sayhiben/little-on-air/release/little-on-air-enclosure-v2.16/reference/README.md

# Drawing and coordinate scope

Use [front-wiring.svg](front-wiring.svg) and [routing-coordinates.json](routing-coordinates.json) for current v2.16 LED routes H1–H4. The nominal lengths are fitting references, not cut lengths. Lane numbers are not electrical pin numbers.

The historical rear coordinates are labeled separately inside the JSON; old H1–H4 coordinates are removed. Existing compact rear leads and junctions must be dressed around the current routes. Older assembly views show interfaces unchanged by v2.16; the `v216-` views show the revised parts.
