sayhiben/little-on-air/hardware/archive/enclosure/v216/README.md

# Archived enclosure v2.16

This rearward-wiring revision changes housing 05 and yoke 06, retaining the
v2.15 frame. The user kept the complete v2.15 case with open-backed frame channels
and restored it as current on September 26, 2026.

- [Current v2.15 case](../../../enclosure/README.md)
- [Preserved v2.16 release](../../../../release/little-on-air-enclosure-v2.16/README.md)
- [Preserved development outputs](../output/v216/)

The archived CAD, print files, reports and scripts retain their bytes. Some
scripts assume their former `hardware/enclosure/v216/` location. Use a separate
checkout of `de26e571f803cca94601db4a099f2a24f3e53c03` for that tooling layout.
The original one-time patch/probe scripts are preserved alongside the final
builder. Published releases and their checksum files retain their existing paths.
