sayhiben/little-on-air/hardware/archive/enclosure/archive/README.md

# Archived loose outputs

Loose generated reports moved out of the repository root during release cleanup are retained here. Historical CAD and fabrication directories keep their original paths under `../output/` because the generation scripts use some of them as inputs.

Use the [current release](../../../release/little-on-air-enclosure-v2.13/README.md) for printing, laser work and assembly.

`2026-09-14-user-layout-before-release.3mf` preserves the original edited three-plate project. It still contains the extra keeper and PETG assignment for the insert; it is historical, not the corrected release print file.
