sayhiben/little-on-air/hardware/controller/igor-desk-v1/output/views/rear.png

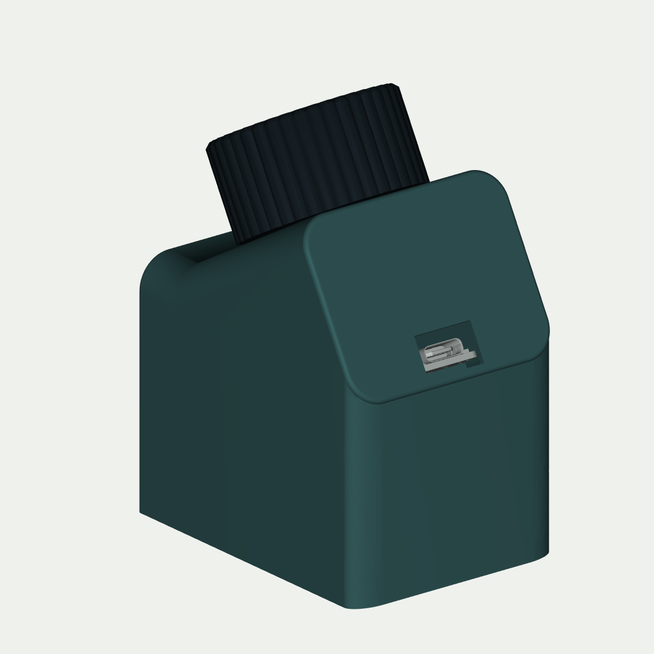
hardware/controller/igor-desk-v1/output/views/rear.png
