sayhiben/little-on-air/hardware/controller/igor-desk-v1/output/views/screen-concept.png

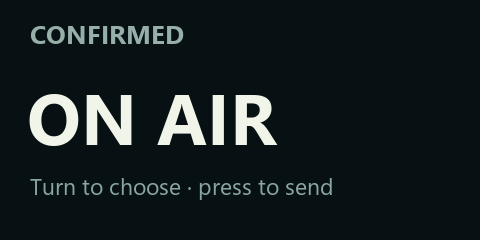
hardware/controller/igor-desk-v1/output/views/screen-concept.png
