sayhiben/little-on-air/hardware/controller/igor-desk-v1/output/views/section.png

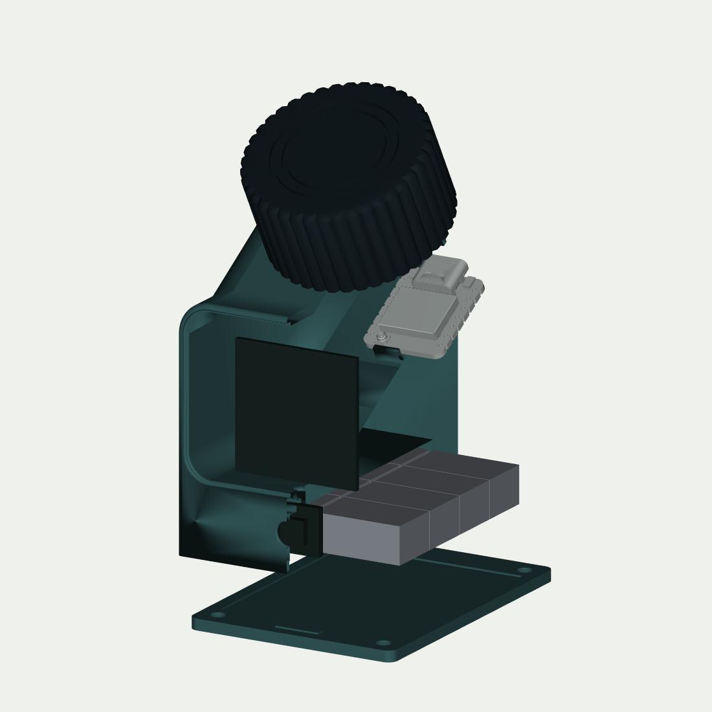
hardware/controller/igor-desk-v1/output/views/section.png
