sayhiben/little-on-air/hardware/controller/igor-desk-v1/output/views/underside.png

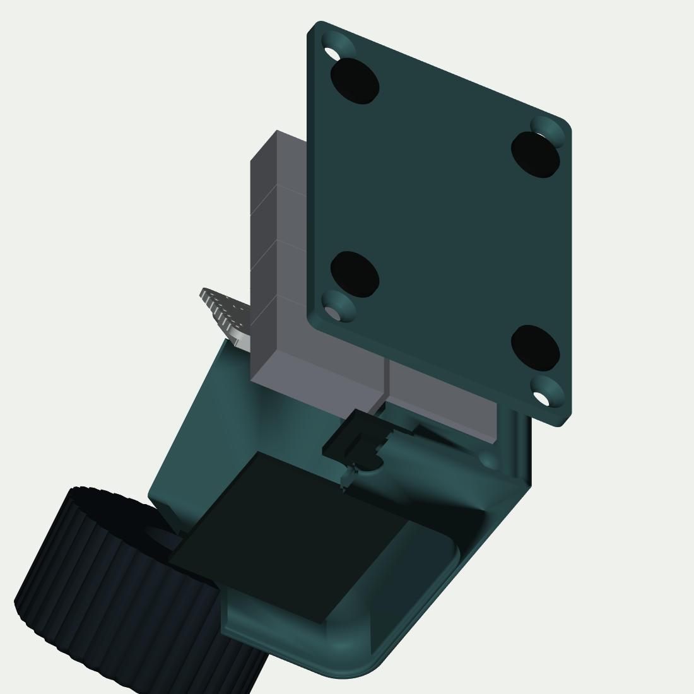
hardware/controller/igor-desk-v1/output/views/underside.png
