sayhiben/little-on-air/hardware/controller/igor-flat-base-v3/output/views/original-side.png

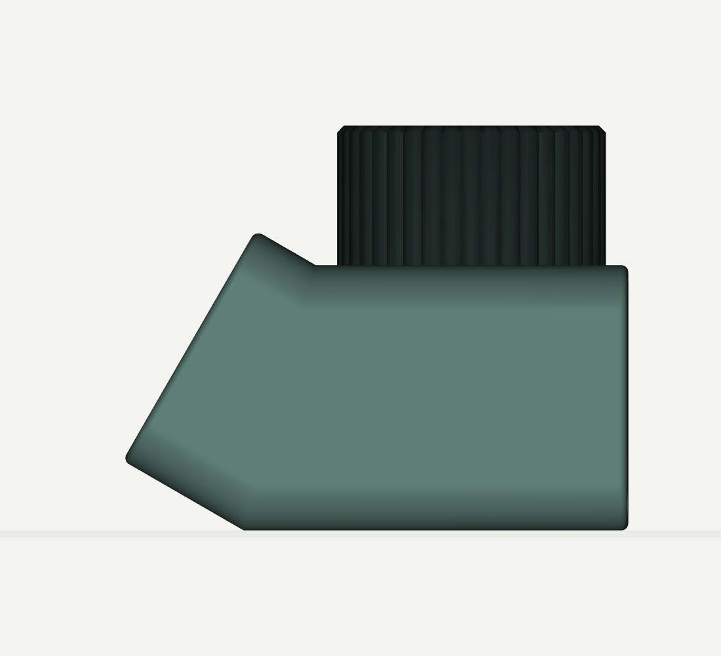
hardware/controller/igor-flat-base-v3/output/views/original-side.png
