sayhiben/little-on-air/hardware/controller/igor-flat-base-v3/output/views/original.png

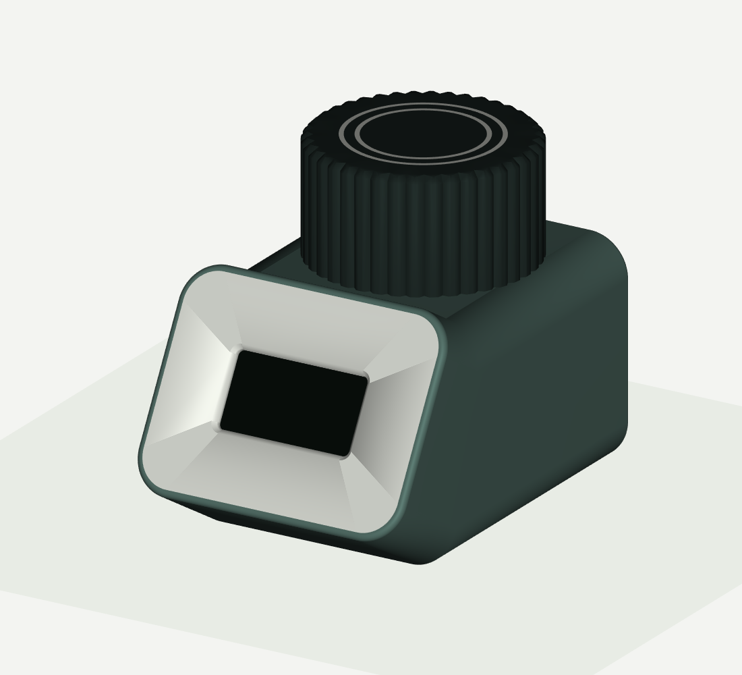
hardware/controller/igor-flat-base-v3/output/views/original.png
