sayhiben/little-on-air/hardware/controller/igor-minimal-v2/output/views/inside.png

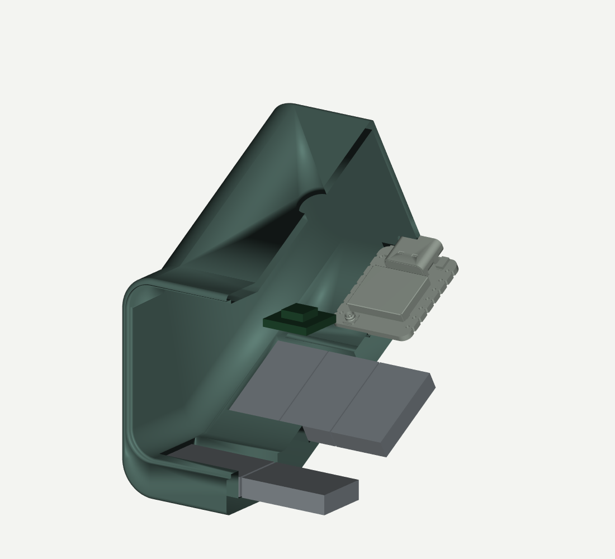
hardware/controller/igor-minimal-v2/output/views/inside.png
