sayhiben/little-on-air/hardware/controller/igor-minimal-v2/output/views/original-side.png

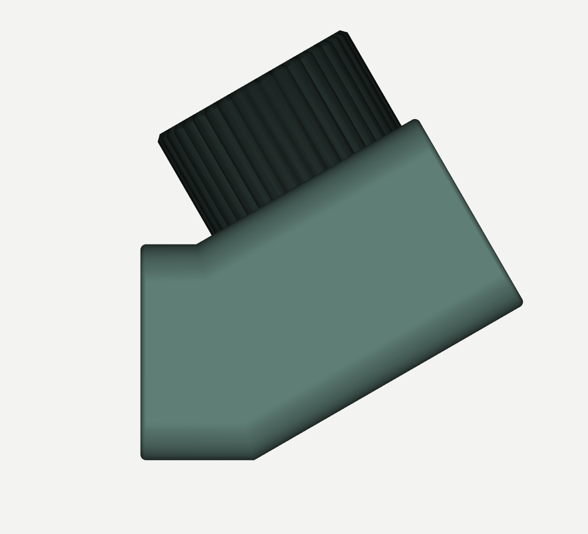
hardware/controller/igor-minimal-v2/output/views/original-side.png
