sayhiben/little-on-air/hardware/controller/igor-minimal-v2/output/views/original.png

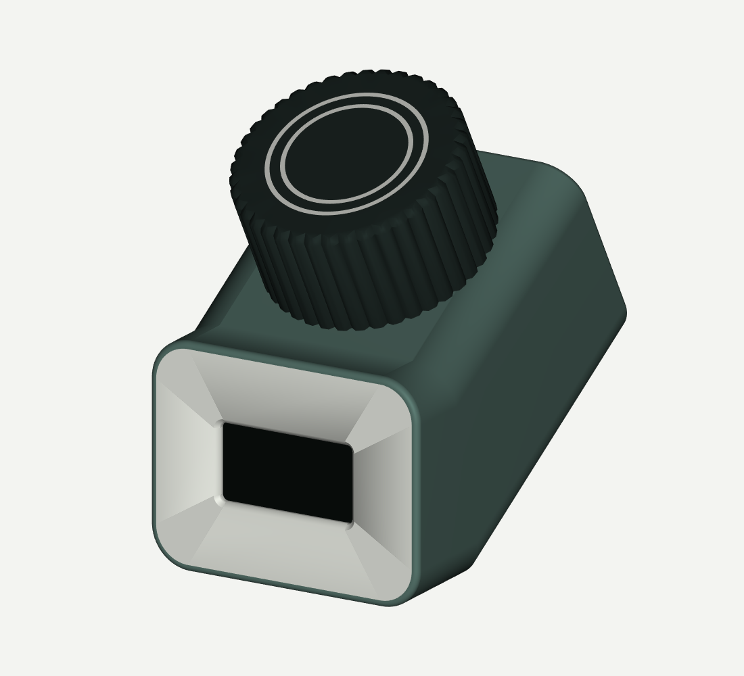
hardware/controller/igor-minimal-v2/output/views/original.png
