sayhiben/little-on-air/hardware/controller/igor-minimal-v2/output/views/revised-side.png

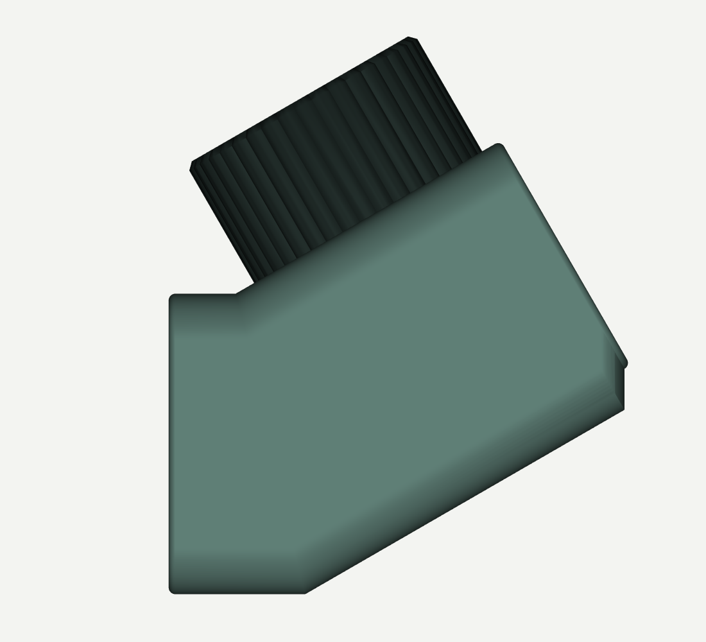
hardware/controller/igor-minimal-v2/output/views/revised-side.png
