sayhiben/little-on-air/hardware/enclosure/output/on-air-v28-fabrication/views/retained-electronics.png

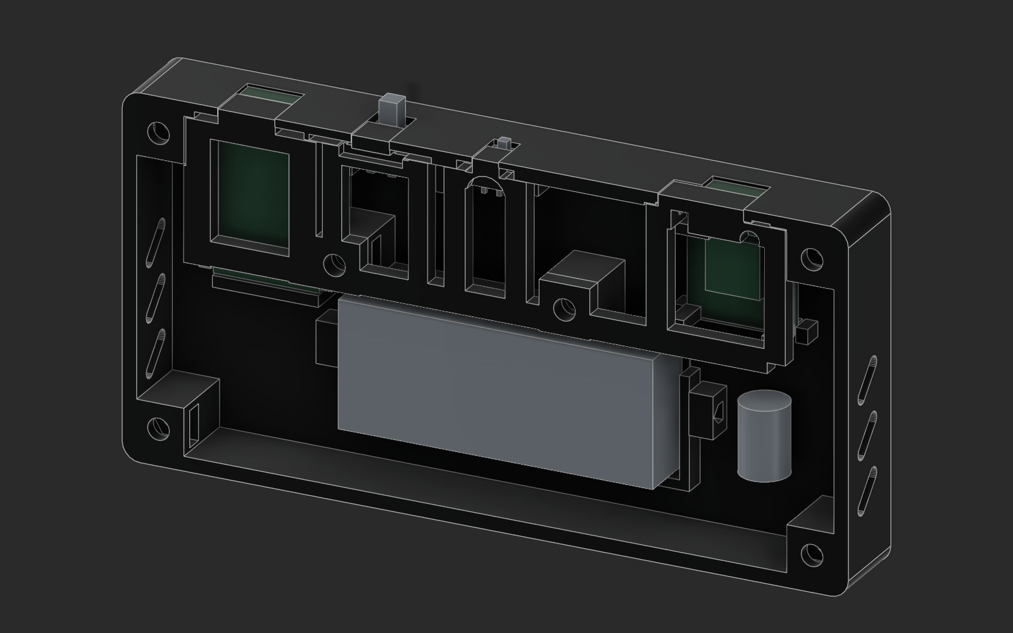
hardware/enclosure/output/on-air-v28-fabrication/views/retained-electronics.png
