sayhiben/little-on-air/hardware/enclosure/output/on-air-v210-beveled-front/views/beveled-frame.png

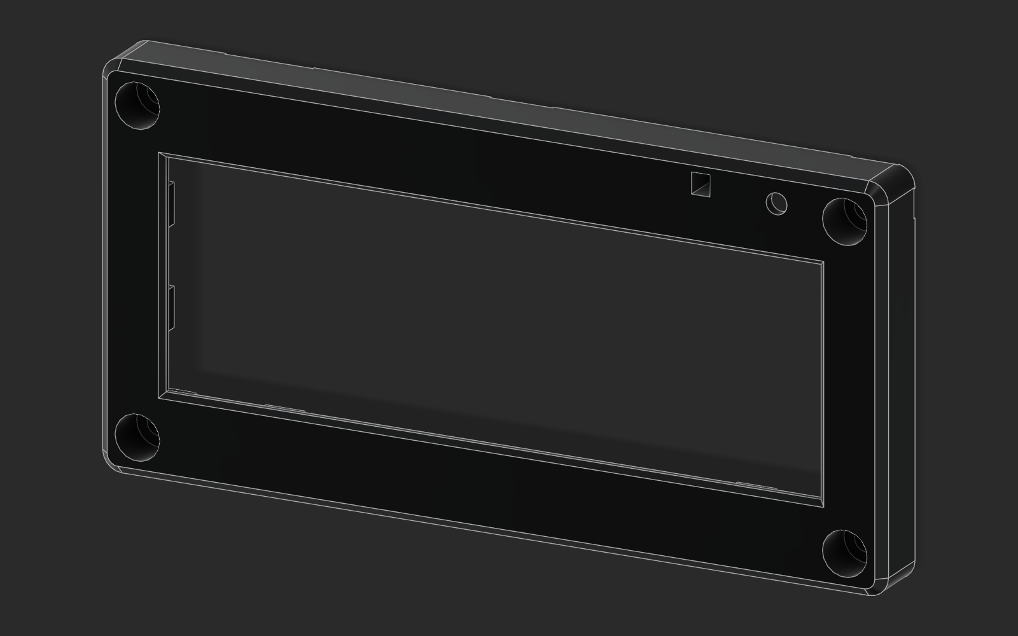
hardware/enclosure/output/on-air-v210-beveled-front/views/beveled-frame.png
