sayhiben/little-on-air/hardware/enclosure/output/on-air-v210-beveled-front/views/beveled-front.png

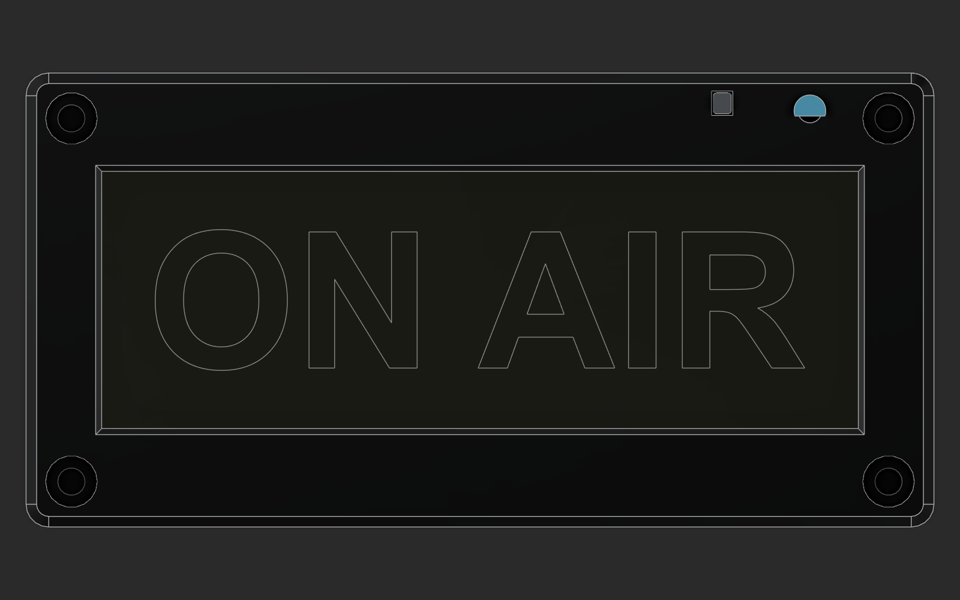
hardware/enclosure/output/on-air-v210-beveled-front/views/beveled-front.png
