sayhiben/little-on-air/hardware/enclosure/output/on-air-v211-clean-top-front/views/clean-top-seam.png

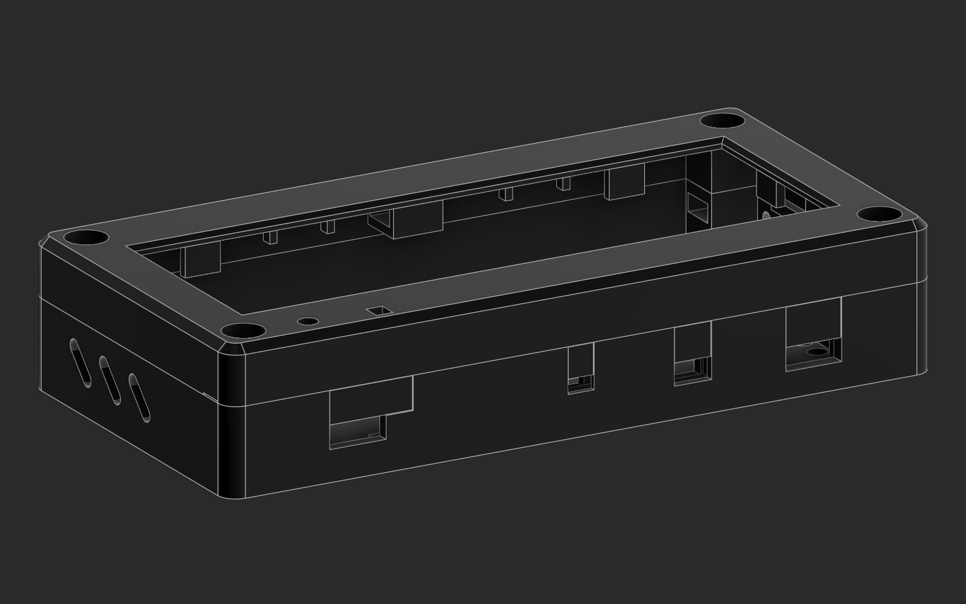
hardware/enclosure/output/on-air-v211-clean-top-front/views/clean-top-seam.png
