sayhiben/little-on-air/hardware/enclosure/output/on-air-v212-clean-perimeter-front/views/clean-right-bottom-seam.png

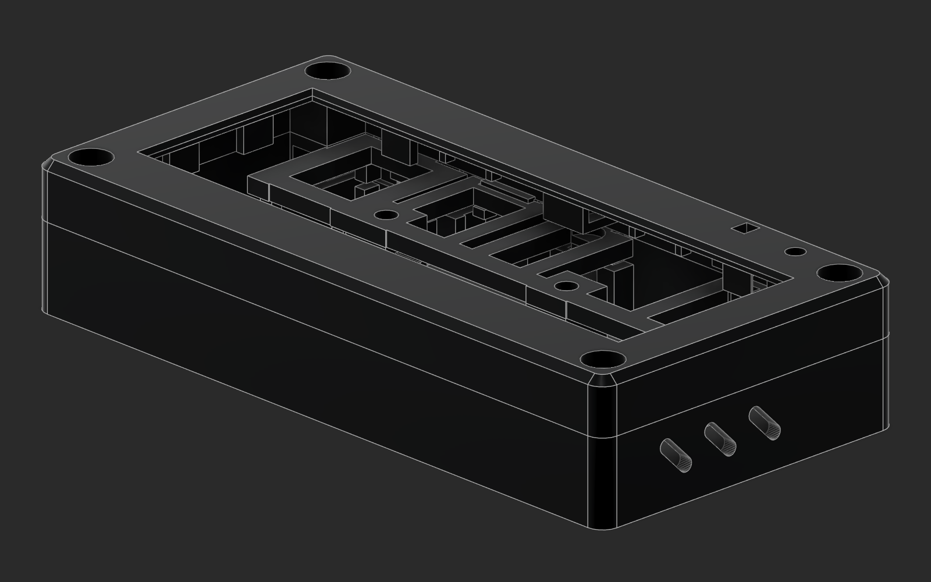
hardware/enclosure/output/on-air-v212-clean-perimeter-front/views/clean-right-bottom-seam.png
