sayhiben/little-on-air/hardware/enclosure/output/on-air-v212-clean-perimeter-front/views/clean-top-left-seam.png

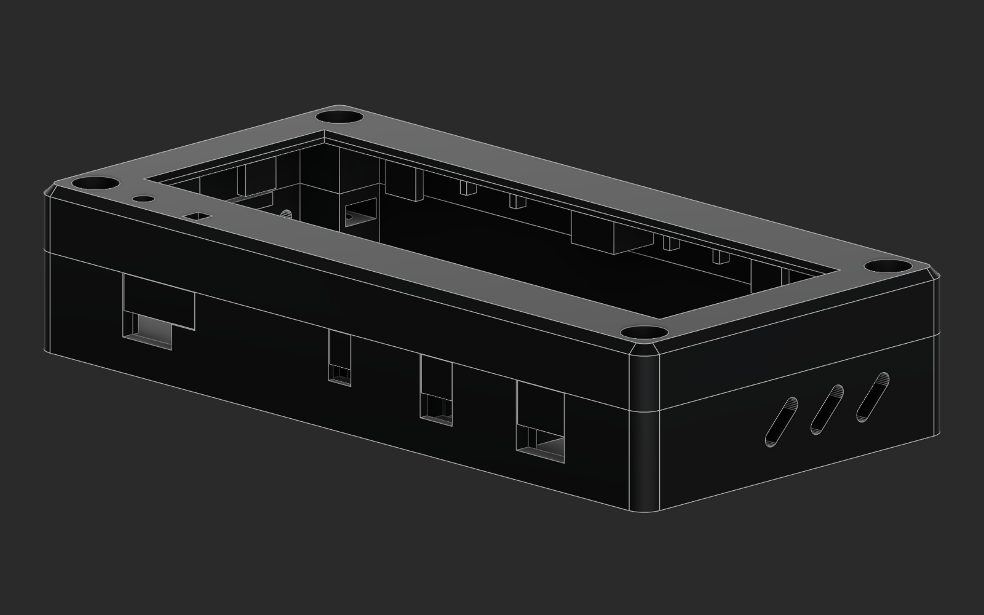
hardware/enclosure/output/on-air-v212-clean-perimeter-front/views/clean-top-left-seam.png
