sayhiben/little-on-air/hardware/enclosure/output/v213-complete/views/plate_1.png

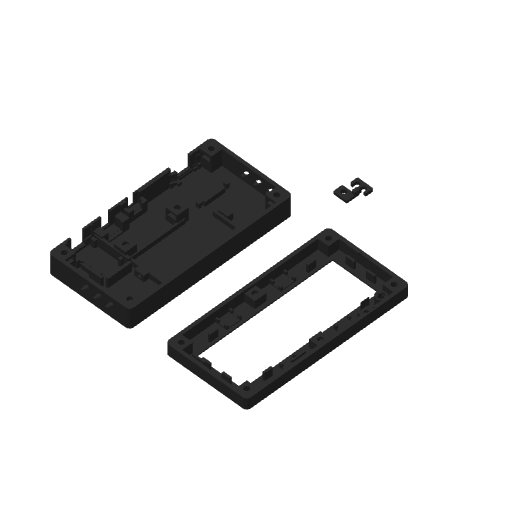
hardware/enclosure/output/v213-complete/views/plate_1.png
