sayhiben/little-on-air/hardware/enclosure/output/v213-complete/views/plate_3.png

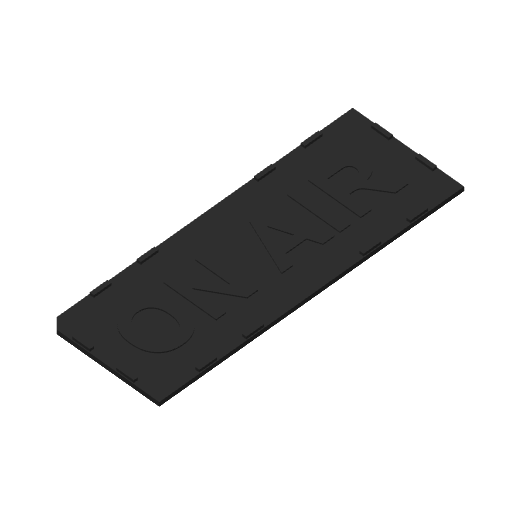
hardware/enclosure/output/v213-complete/views/plate_3.png
