sayhiben/little-on-air/hardware/enclosure/output/v216/adafruit-side-strip-reference.jpg

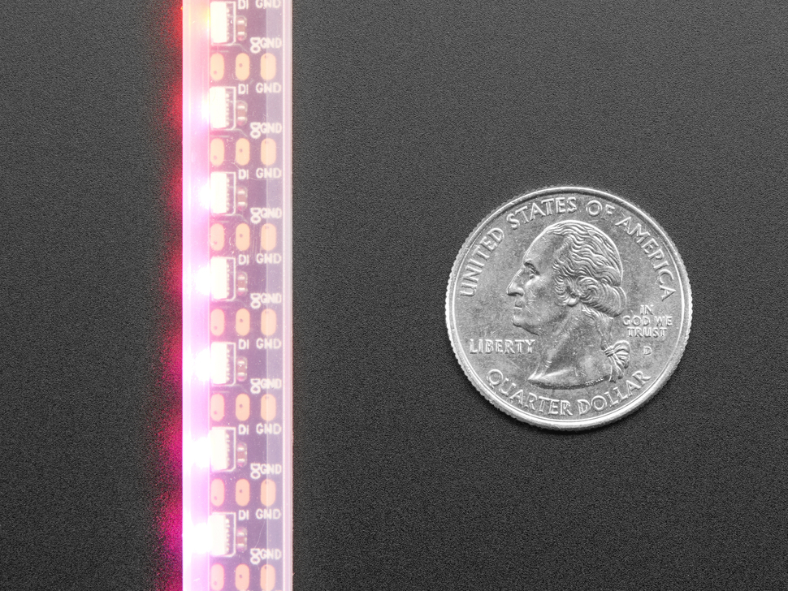
hardware/enclosure/output/v216/adafruit-side-strip-reference.jpg
