sayhiben/little-on-air/hardware/enclosure/output/v216/existing-sections.png

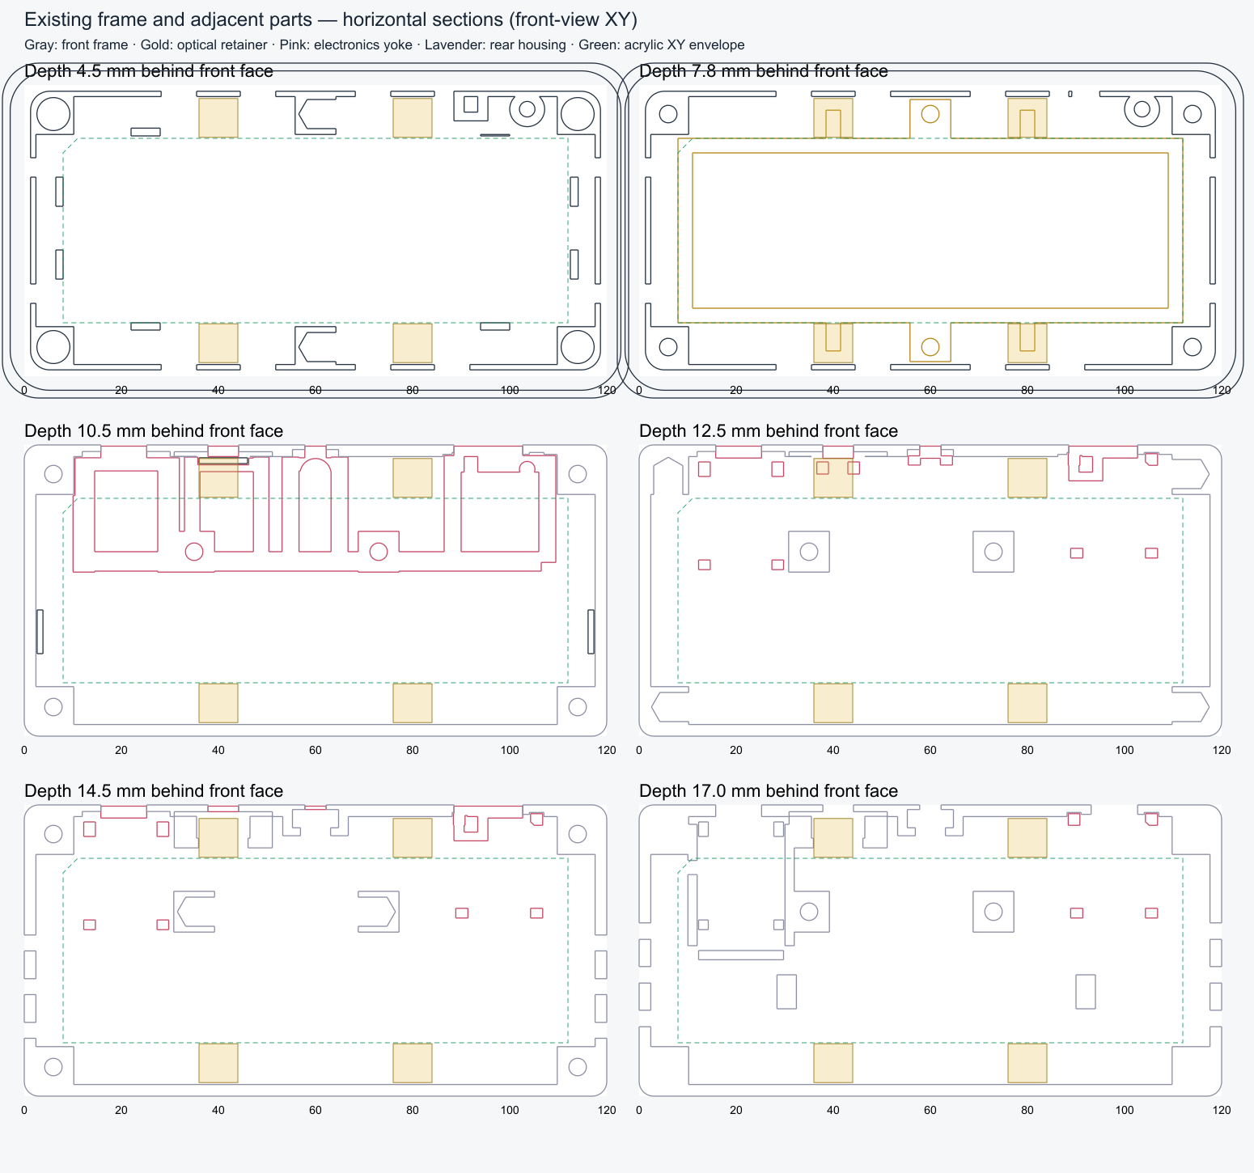
hardware/enclosure/output/v216/existing-sections.png
