sayhiben/little-on-air/hardware/enclosure/output/v216/views/frame-unchanged.png

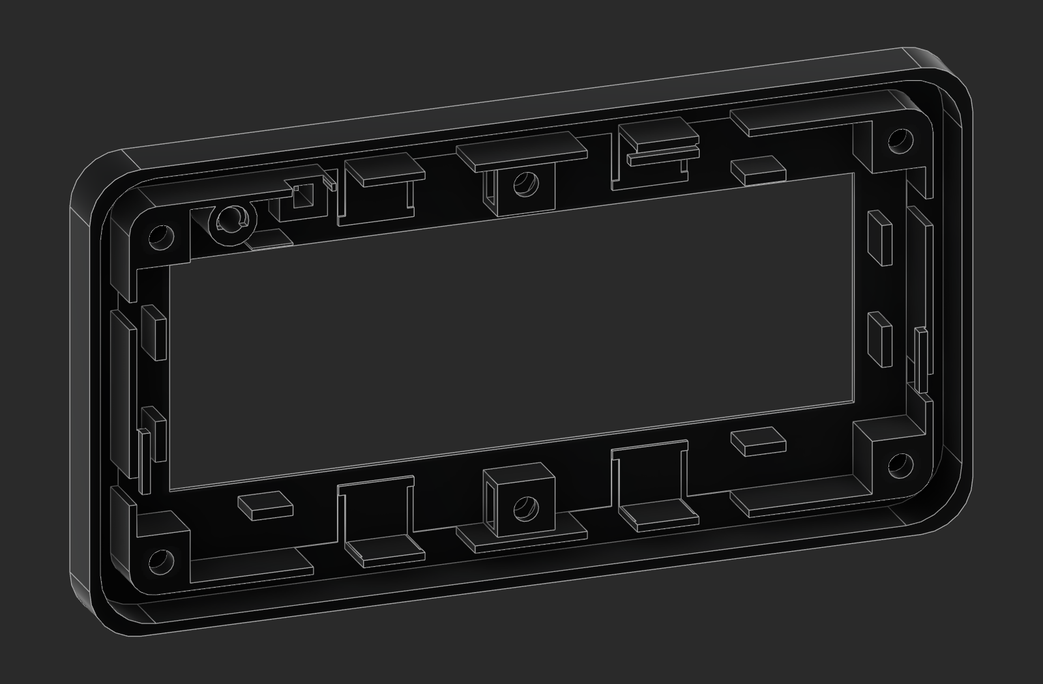
hardware/enclosure/output/v216/views/frame-unchanged.png
