sayhiben/little-on-air/hardware/enclosure/output/views/electronics-layout.png

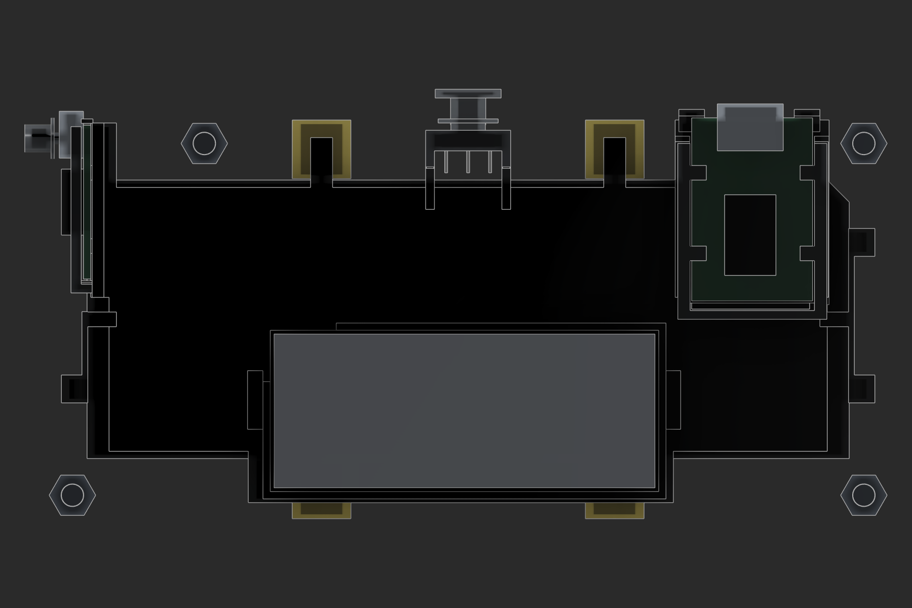
hardware/enclosure/output/views/electronics-layout.png
