sayhiben/little-on-air/hardware/enclosure/output/views/front.png

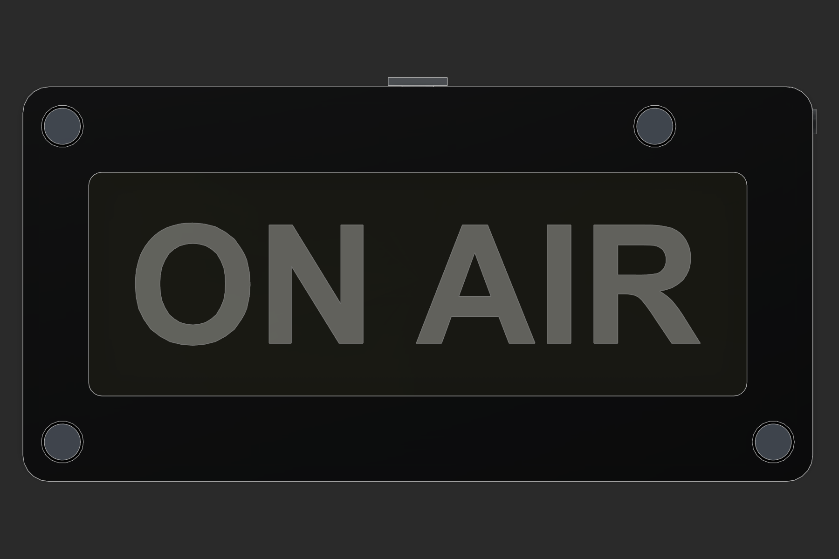
hardware/enclosure/output/views/front.png
