sayhiben/little-on-air/hardware/enclosure/output/views/rear-service.png

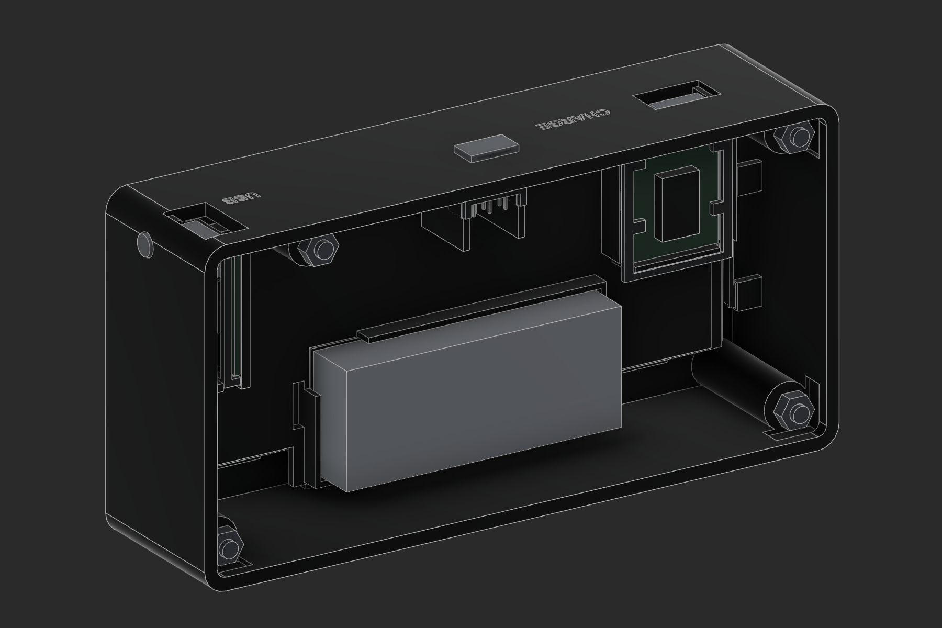
hardware/enclosure/output/views/rear-service.png
