sayhiben/little-on-air/release/little-on-air-enclosure-v2.16/reference/previews/91-kerf-plug-and-frame-CUT.png

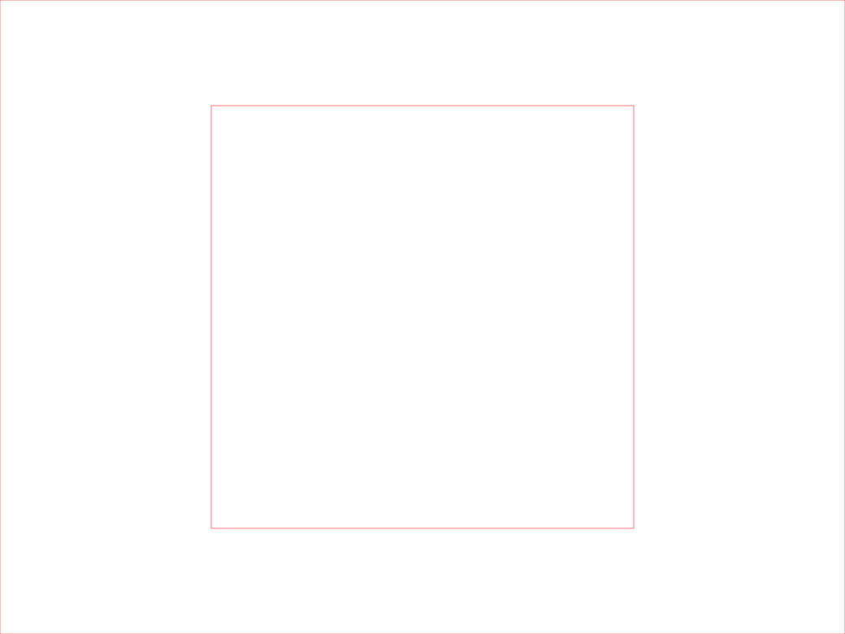
release/little-on-air-enclosure-v2.16/reference/previews/91-kerf-plug-and-frame-CUT.png
