sayhiben/little-on-air/release/little-on-air-enclosure-v2.16/reference/previews/92-engraving-quality-nine-samples-FILL.png

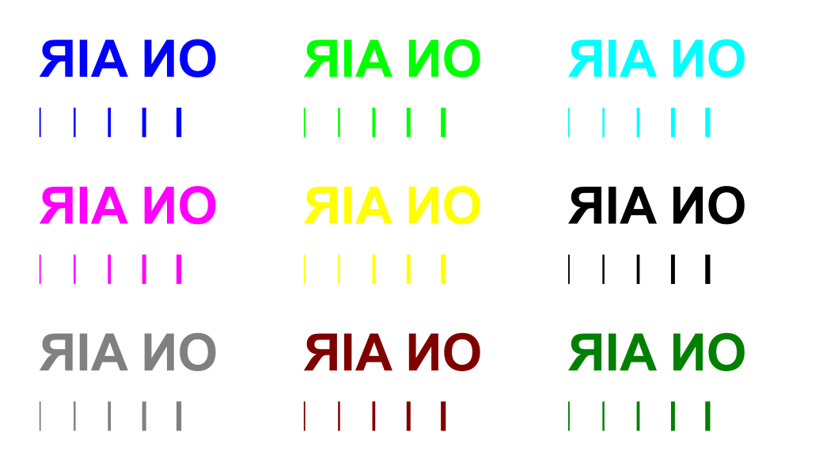
release/little-on-air-enclosure-v2.16/reference/previews/92-engraving-quality-nine-samples-FILL.png
