sayhiben/little-on-air/release/little-on-air-enclosure-v2.16/reference/views/rear-housing-with-retention.png

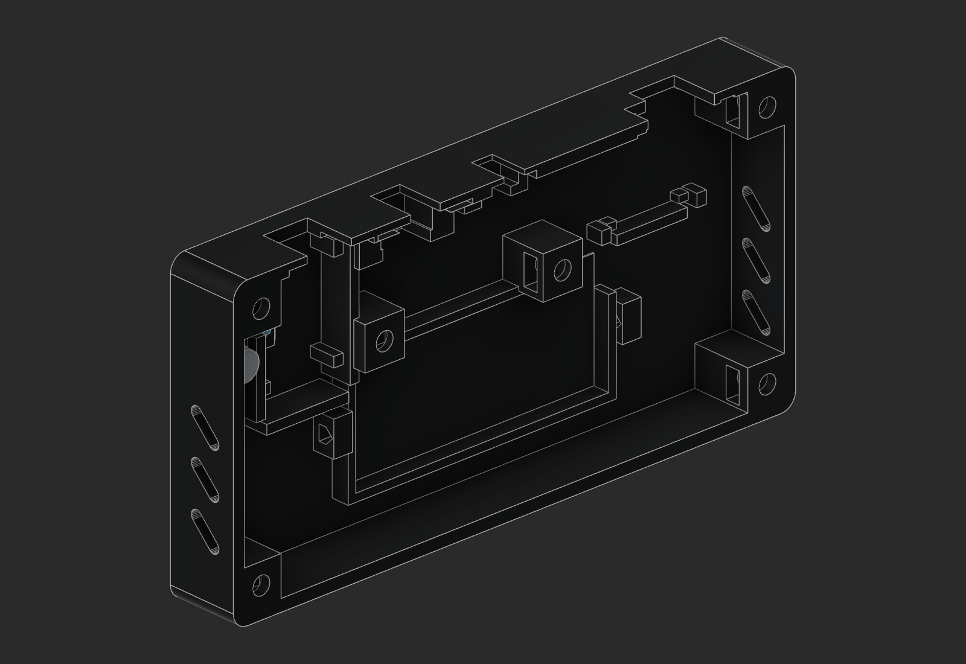
release/little-on-air-enclosure-v2.16/reference/views/rear-housing-with-retention.png
