sayhiben/little-on-air/hardware/controller/igor-measured-v4/output/assembly-meshes/encoder-box.stl

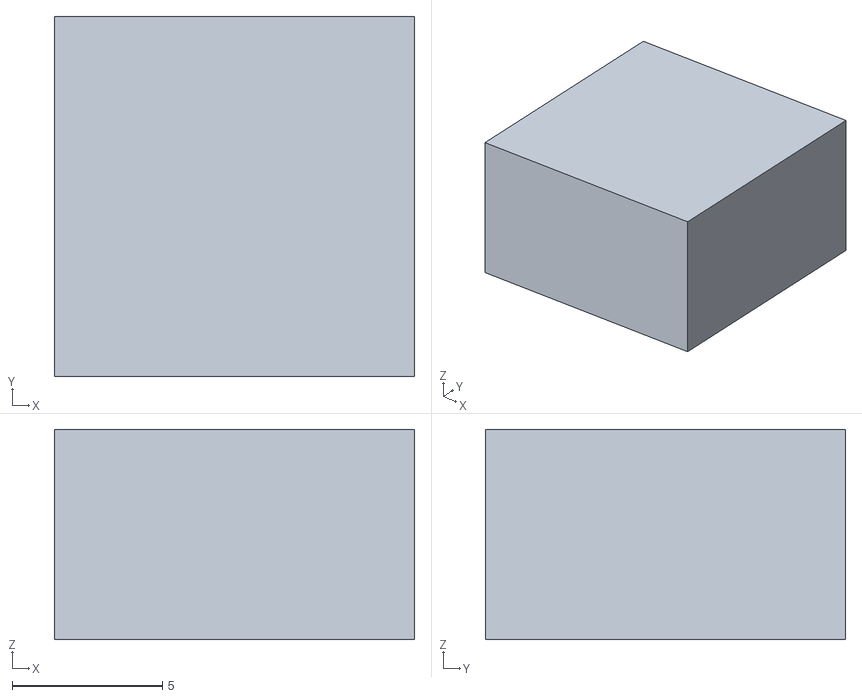
[picture p55: CAD file, 2026-09-26]
hardware/controller/igor-measured-v4/output/assembly-meshes/encoder-box.stl
12.0 x 12.0 x 7.00
