sayhiben/little-on-air/hardware/controller/igor-measured-v4/output/bambu-studio/igor-measured-v4-X1C-PLA-face-cassette-inlays.3mf

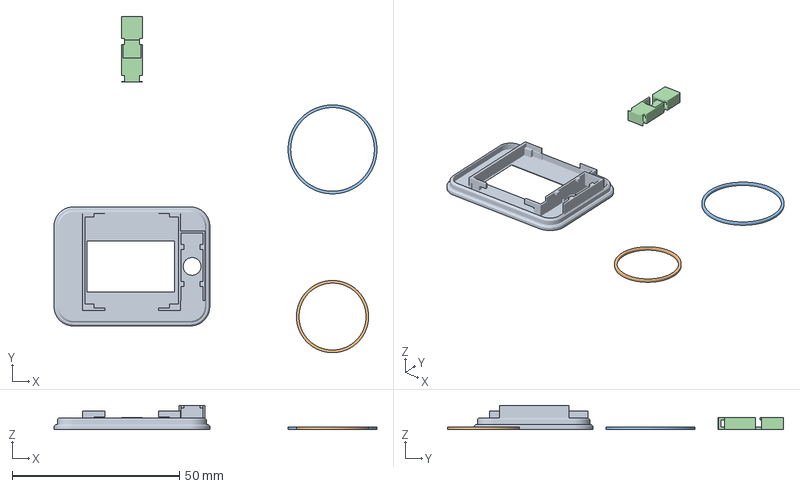
[picture p56: CAD file, 2026-09-26]
hardware/controller/igor-measured-v4/output/bambu-studio/igor-measured-v4-X1C-PLA-face-cassette-inlays.3mf
96.6 x 100.6 x 7.20 mm
02-igor-measured-faceplate.stl
04-igor-small-inlay-original.stl
05-igor-large-inlay-original.stl
07-strip-cassette.stl
