sayhiben/little-on-air/hardware/controller/igor-measured-v4/output/cad/06-front-diffuser-PETG.step

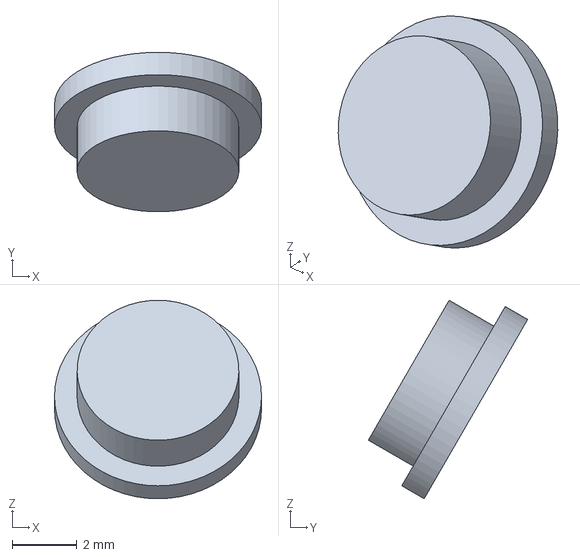
[picture p57: CAD file, 2026-09-26]
hardware/controller/igor-measured-v4/output/cad/06-front-diffuser-PETG.step
6.40 x 4.93 x 6.14 mm
