sayhiben/little-on-air/hardware/controller/igor-measured-v4/output/reference-components/weight-right.step

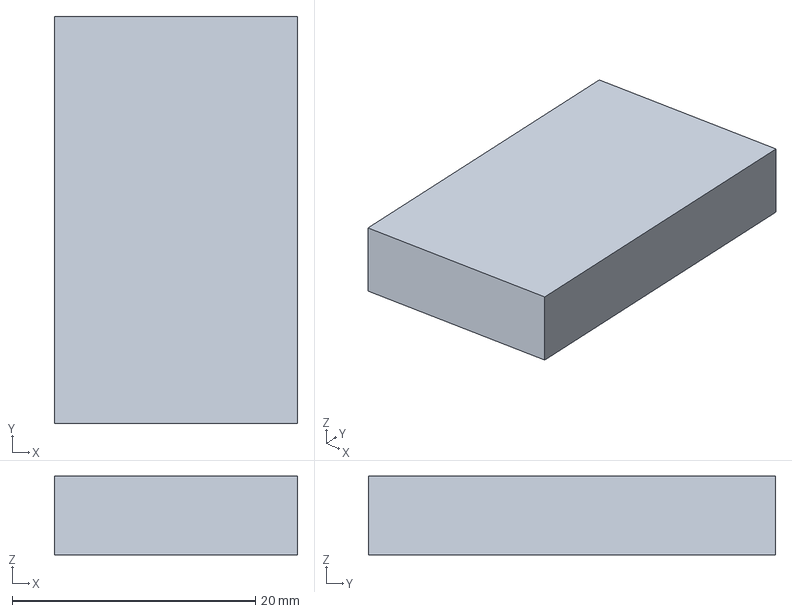
[picture p58: CAD file, 2026-09-26]
hardware/controller/igor-measured-v4/output/reference-components/weight-right.step
20.0 x 33.5 x 6.50 mm
