sayhiben/little-on-air/hardware/controller/igor-minimal-v2/output/assembly-meshes/weight-reference.stl

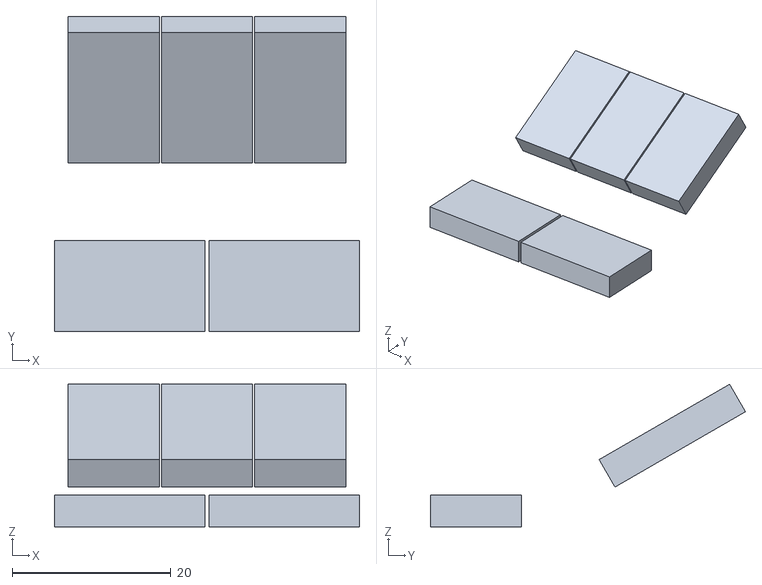
[picture p59: CAD file, 2026-09-26]
hardware/controller/igor-minimal-v2/output/assembly-meshes/weight-reference.stl
38.5 x 39.7 x 18.0
