sayhiben/little-on-air/hardware/controller/igor-minimal-v2/output/bambu-studio/igor-minimal-v2-X1C-PLA-face-inlays.3mf

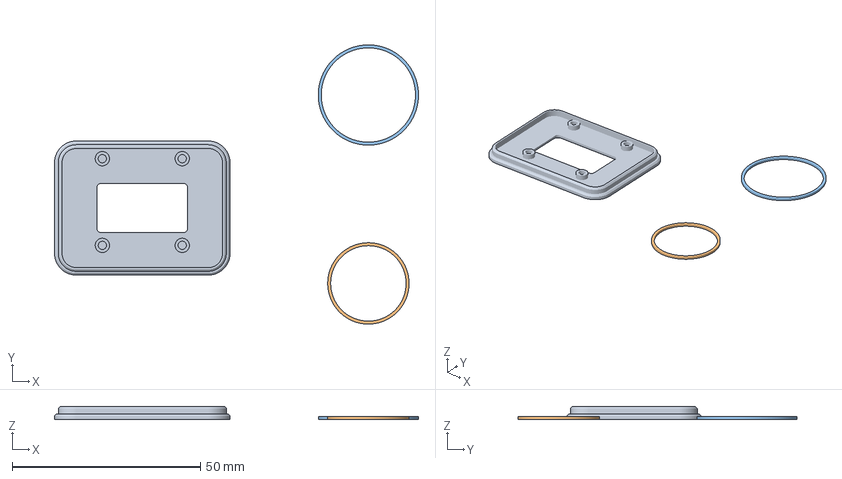
[picture p60: CAD file, 2026-09-26]
hardware/controller/igor-minimal-v2/output/bambu-studio/igor-minimal-v2-X1C-PLA-face-inlays.3mf
96.6 x 74.1 x 3.50 mm
02-igor-faceplate-original.stl
04-igor-small-inlay-original.stl
05-igor-large-inlay-original.stl
