sayhiben/little-on-air/hardware/enclosure/output/bambu-studio/ams-verified/little-on-air-X1C-PETG-AMS.3mf

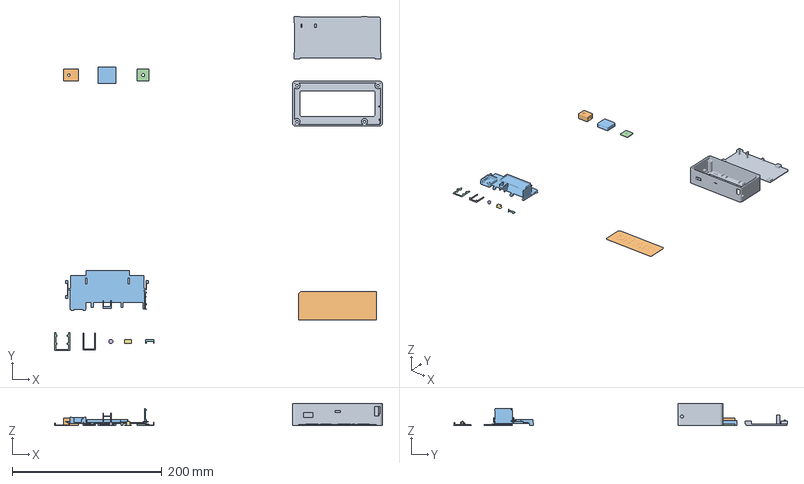
[picture p61: CAD file, 2026-09-26]
hardware/enclosure/output/bambu-studio/ams-verified/little-on-air-X1C-PETG-AMS.3mf
437.4 x 445.4 x 30.0 mm
01-body-and-front-frame.stl
03-black-and-white-backing.stl
04-optical-and-electronics-tray.stl
05-charger-keeper.stl
06-xiao-keeper.stl
07-captive-reset-plunger.stl
08-captive-power-slider.stl
09-switch-keeper.stl
10-wall-back-plate.stl
90-m3-head-and-nut-fit-sample.stl
91-led-and-acrylic-fit-sample.stl
92-reset-guide-fit-sample.stl
