sayhiben/little-on-air/hardware/enclosure/output/bambu-studio/input/07-captive-reset-plunger.stl

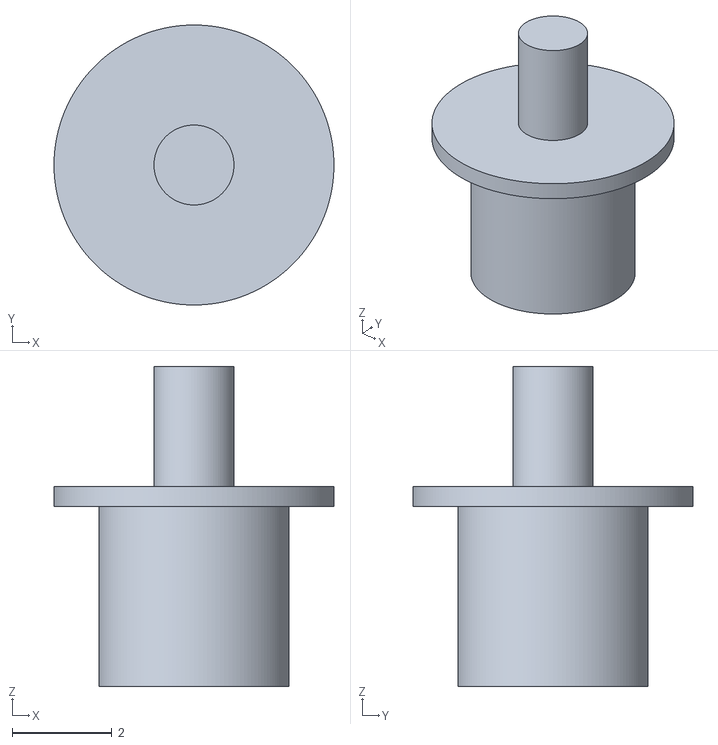
[picture p62: CAD file, 2026-09-26]
hardware/enclosure/output/bambu-studio/input/07-captive-reset-plunger.stl
5.60 x 5.60 x 6.40
