sayhiben/little-on-air/hardware/enclosure/output/bambu-studio/manual-sliced/little-on-air-X1C-PETG-manual-swap-sliced.3mf

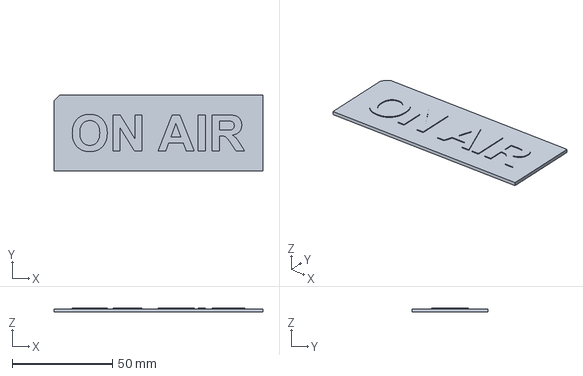
[picture p63: CAD file, 2026-09-26]
hardware/enclosure/output/bambu-studio/manual-sliced/little-on-air-X1C-PETG-manual-swap-sliced.3mf
104.0 x 38.0 x 2.00 mm
