sayhiben/little-on-air/hardware/enclosure/output/design-review/references/top.dxf

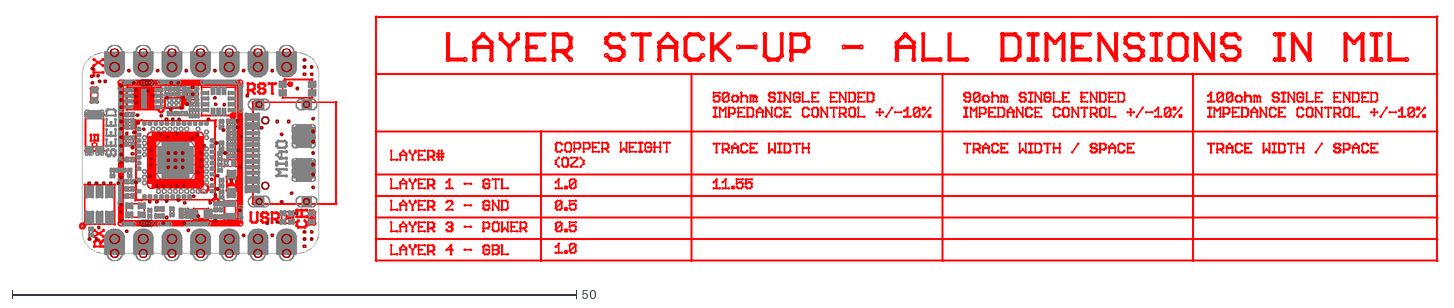
[picture p64: CAD file, 2026-09-26]
hardware/enclosure/output/design-review/references/top.dxf
125.9 x 22.3
