sayhiben/little-on-air/hardware/enclosure/output/fdm-and-acrylic/stl/04-optical-and-electronics-tray.stl

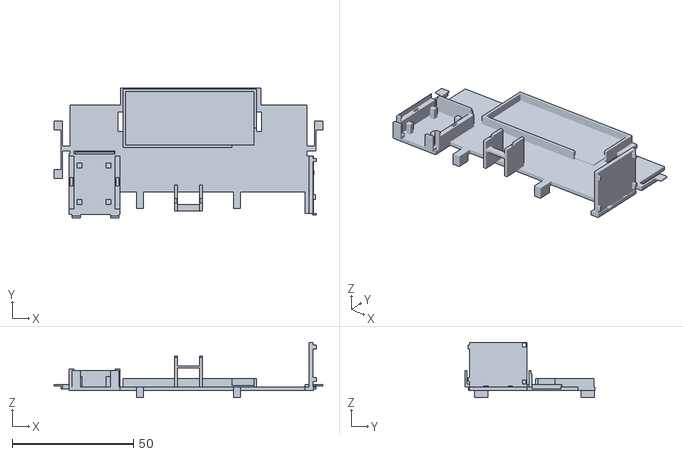
[picture p65: CAD file, 2026-09-26]
hardware/enclosure/output/fdm-and-acrylic/stl/04-optical-and-electronics-tray.stl
111.0 x 53.7 x 22.9
