sayhiben/little-on-air/hardware/enclosure/output/laser/on-air-front-master.dxf

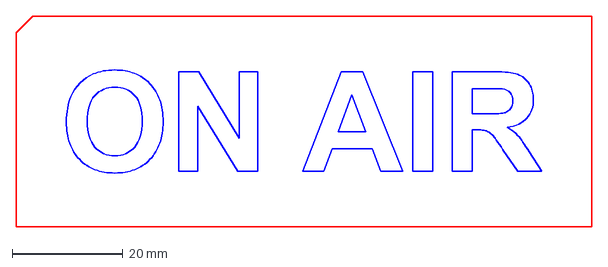
[picture p66: CAD file, 2026-09-26]
hardware/enclosure/output/laser/on-air-front-master.dxf
104.0 x 38.0 mm
