sayhiben/little-on-air/hardware/enclosure/output/little-on-air-fdm-and-acrylic/stl/06-xiao-keeper.stl

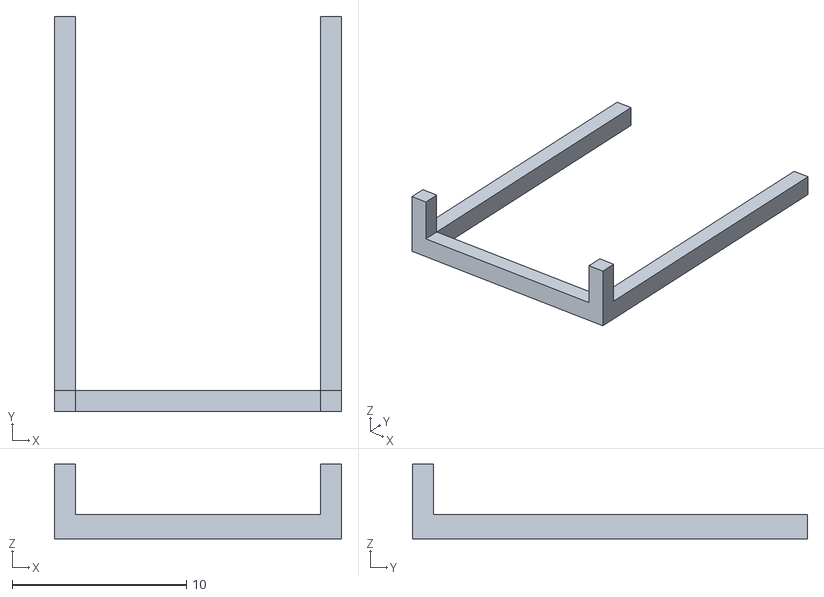
[picture p67: CAD file, 2026-09-26]
hardware/enclosure/output/little-on-air-fdm-and-acrylic/stl/06-xiao-keeper.stl
16.5 x 22.7 x 4.30
