sayhiben/little-on-air/hardware/enclosure/output/on-air-v210-beveled-front/bambu-studio/on-air-v210-X1C-PETG-beveled-front.3mf

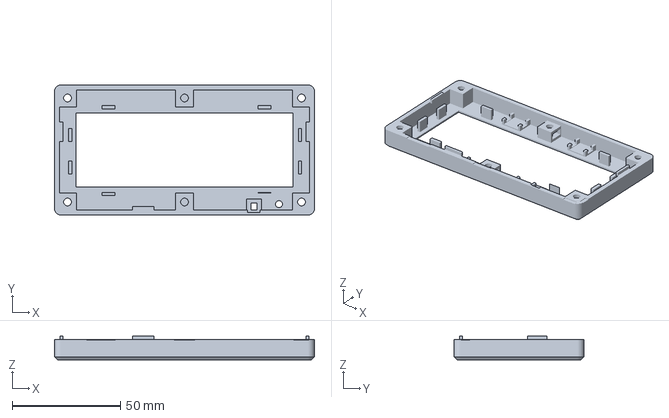
[picture p68: CAD file, 2026-09-26]
hardware/enclosure/output/on-air-v210-beveled-front/bambu-studio/on-air-v210-X1C-PETG-beveled-front.3mf
120.0 x 60.0 x 11.0 mm
