sayhiben/little-on-air/hardware/enclosure/output/on-air-v213-captive-light-guides/bambu-studio/on-air-v213-clear-PETG-three-light-guides.3mf

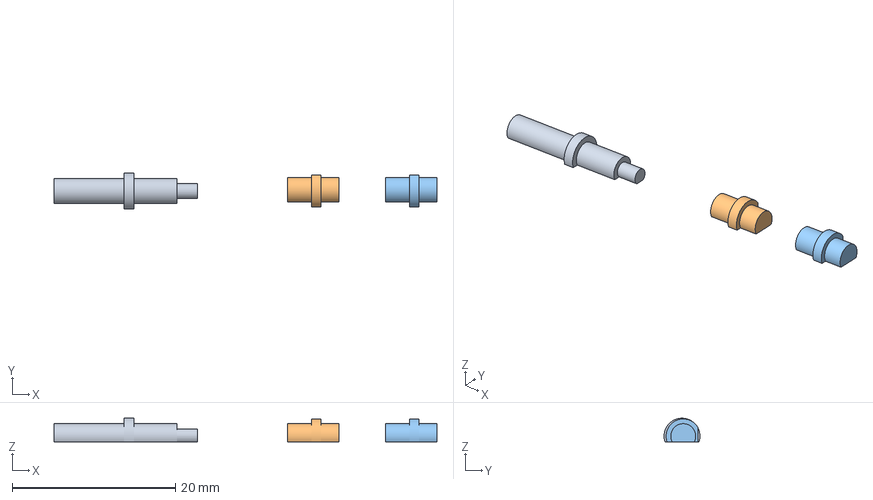
[picture p69: CAD file, 2026-09-26]
hardware/enclosure/output/on-air-v213-captive-light-guides/bambu-studio/on-air-v213-clear-PETG-three-light-guides.3mf
46.9 x 4.40 x 2.90 mm
08-captive-front-rgb-guide.stl
09-charger-light-guide.stl x 2
