sayhiben/little-on-air/hardware/enclosure/output/on-air-v213-captive-light-guides/stl/08-captive-front-rgb-guide.stl

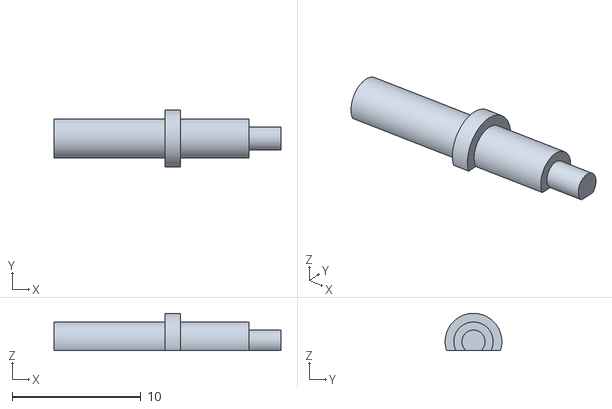
[picture p70: CAD file, 2026-09-26]
hardware/enclosure/output/on-air-v213-captive-light-guides/stl/08-captive-front-rgb-guide.stl
17.6 x 4.40 x 2.90
