sayhiben/little-on-air/hardware/enclosure/output/on-air-v22-first-layer-recovery/on-air-v22-X1C-eSUN-PLA-plus-fit-NO-FIRST-LAYER-SCAN.3mf

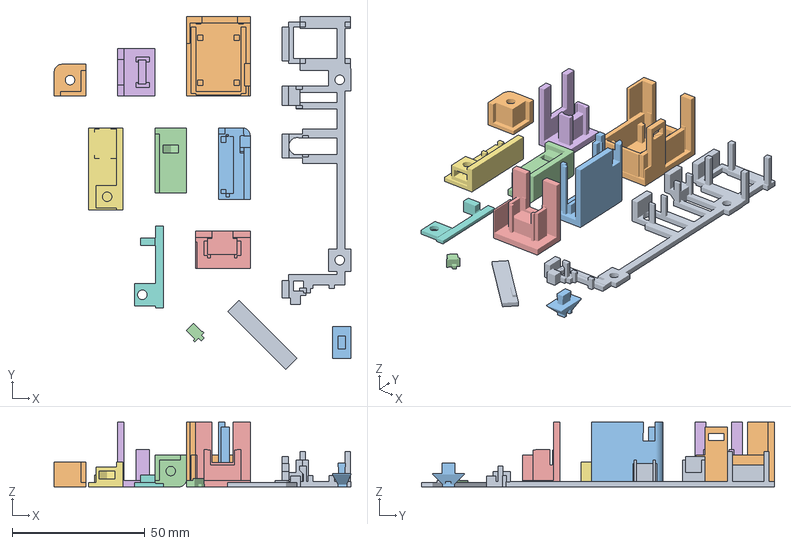
[picture p72: CAD file, 2026-09-26]
hardware/enclosure/output/on-air-v22-first-layer-recovery/on-air-v22-X1C-eSUN-PLA-plus-fit-NO-FIRST-LAYER-SCAN.3mf
112.0 x 133.2 x 24.5 mm
06-electronics-retaining-yoke.stl
92-charger-fit-section.stl
93-XIAO-and-reset-fit-section.stl
90-rear-nut-boss-section.stl
98-SPDT-power-fit-section.stl
94-DPDT-fit-section.stl
95-optical-bezel-section.stl
96-optical-retainer-section.stl
97-optical-spacing-section.stl
91-front-screw-recess-section.stl
08-captive-run-program-slider.stl
07-captive-reset-plunger.stl
