sayhiben/little-on-air/hardware/enclosure/output/on-air-v28-fabrication/bambu-studio/on-air-v28-X1C-eSUN-PLA-plus-manual-swap.3mf

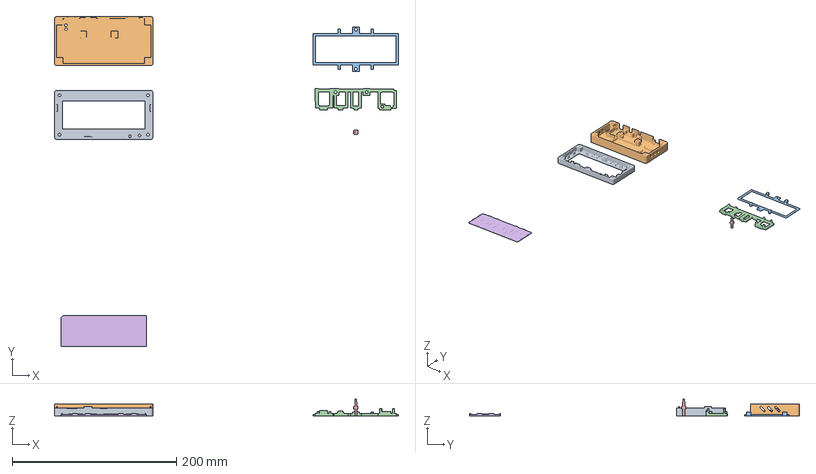
[picture p73: CAD file, 2026-09-26]
hardware/enclosure/output/on-air-v28-fabrication/bambu-studio/on-air-v28-X1C-eSUN-PLA-plus-manual-swap.3mf
419.2 x 402.2 x 20.1 mm
01-front-optical-bezel.stl
05-rear-electronics-housing.stl
04-optical-retainer.stl
06-electronics-retaining-yoke.stl
07-front-guided-reset-button.stl
03-registered-graphic-backing.stl
