sayhiben/little-on-air/hardware/enclosure/output/on-air-v28-fabrication/fit-samples/95-optical-bezel-section.stl

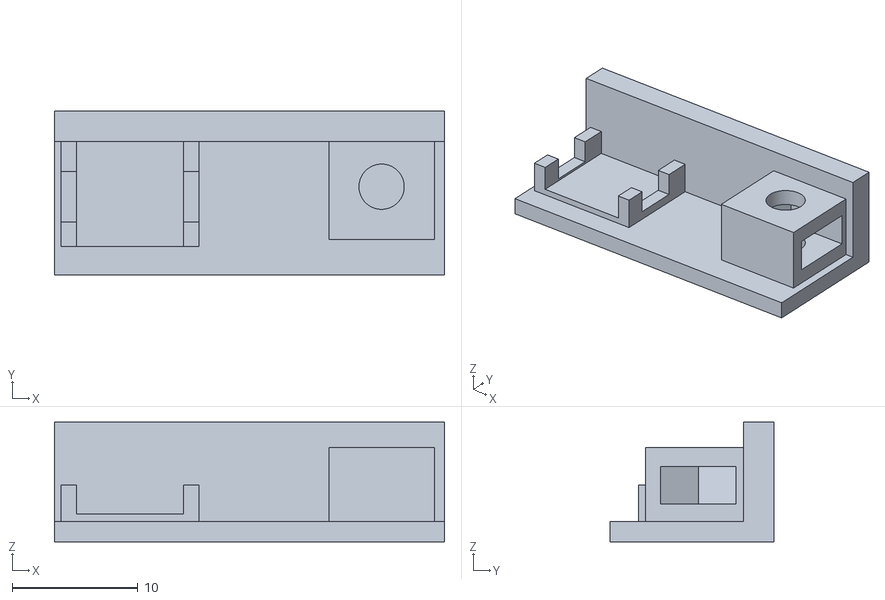
[picture p74: CAD file, 2026-09-26]
hardware/enclosure/output/on-air-v28-fabrication/fit-samples/95-optical-bezel-section.stl
31.0 x 13.0 x 9.50
