sayhiben/little-on-air/hardware/enclosure/output/on-air-v28-fabrication/optional-laminate/82-laminate-rear-shim.stl

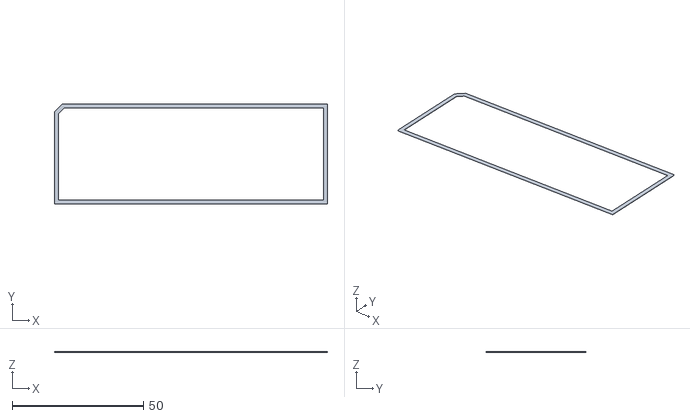
[picture p75: CAD file, 2026-09-26]
hardware/enclosure/output/on-air-v28-fabrication/optional-laminate/82-laminate-rear-shim.stl
104.0 x 38.0 x 0.4
