sayhiben/little-on-air/hardware/enclosure/output/on-air-v28-light-pipes/bambu-studio/on-air-v28-clear-PETG-light-pipes.3mf

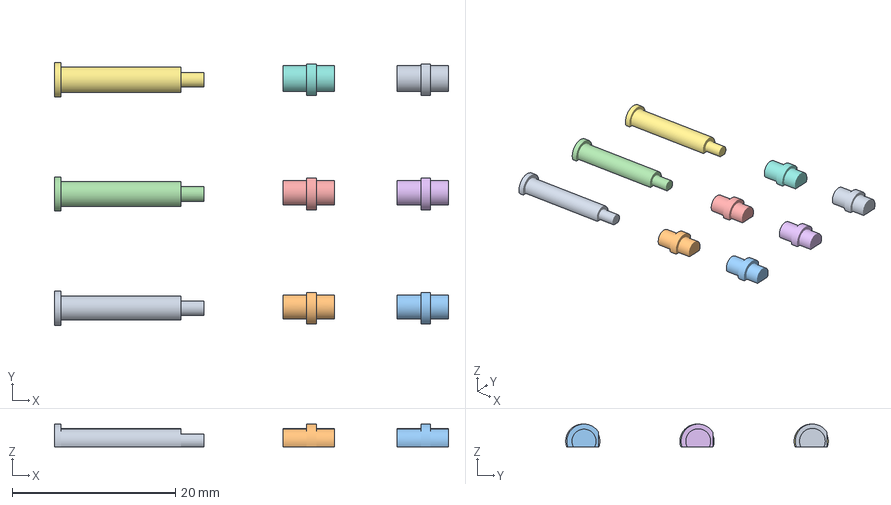
[picture p76: CAD file, 2026-09-26]
hardware/enclosure/output/on-air-v28-light-pipes/bambu-studio/on-air-v28-clear-PETG-light-pipes.3mf
48.3 x 32.2 x 2.80 mm
08-front-rgb-2.95mm.stl
09-charger-2.95mm.stl x 2
08-front-rgb-3.05mm.stl
09-charger-3.05mm.stl x 2
08-front-rgb-3.15mm.stl
09-charger-3.15mm.stl x 2
