sayhiben/little-on-air/hardware/enclosure/output/on-air-v28-light-pipes/stl/08-front-rgb-3.05mm.stl

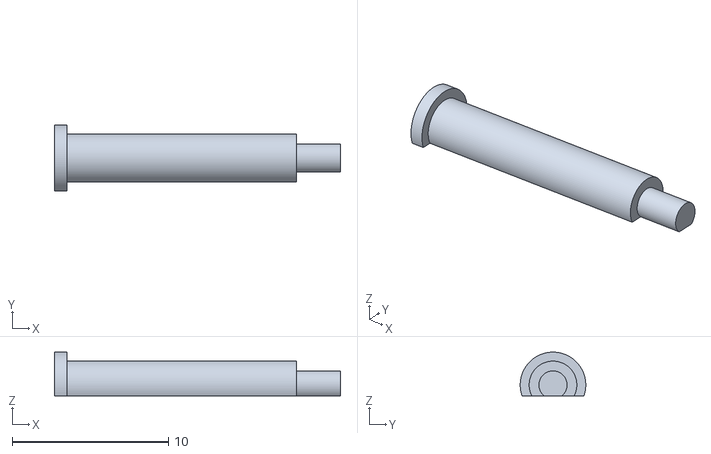
[picture p77: CAD file, 2026-09-26]
hardware/enclosure/output/on-air-v28-light-pipes/stl/08-front-rgb-3.05mm.stl
18.3 x 4.20 x 2.80
