sayhiben/little-on-air/hardware/enclosure/output/print/09-switch-keeper.3mf

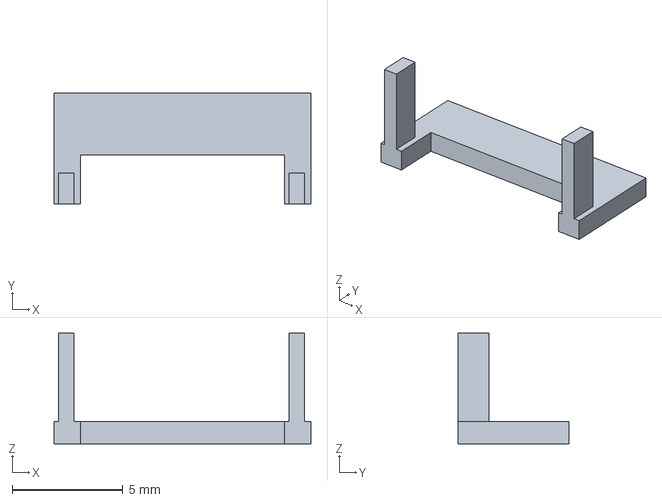
[picture p78: CAD file, 2026-09-26]
hardware/enclosure/output/print/09-switch-keeper.3mf
11.6 x 5.00 x 5.00 mm
