sayhiben/little-on-air/hardware/enclosure/output/v213-complete/on-air-v213-X1C-all-plates.3mf

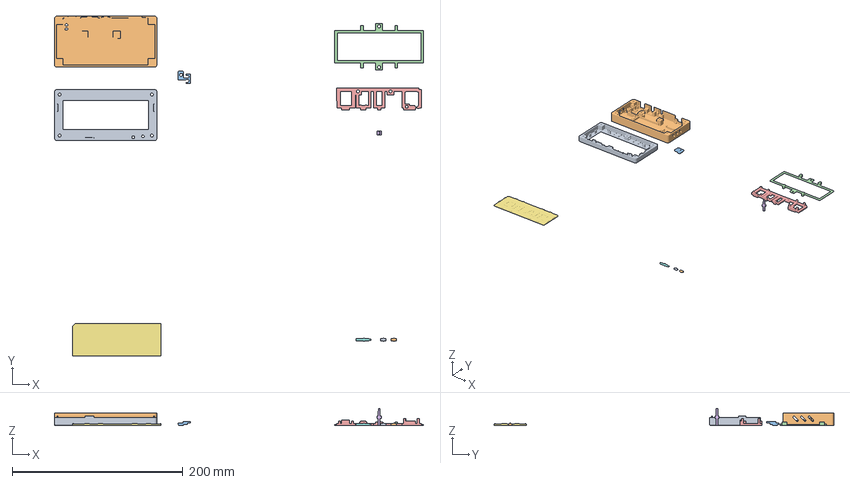
[picture p79: CAD file, 2026-09-26]
hardware/enclosure/output/v213-complete/on-air-v213-X1C-all-plates.3mf
432.2 x 398.2 x 20.1 mm
01-front-optical-bezel.stl
05-rear-electronics-housing.stl
11-rear-light-guide-keeper.stl
04-optical-retainer.stl
06-electronics-retaining-yoke.stl
07-front-guided-reset-button.stl
03-registered-graphic-backing.stl
08-captive-front-rgb-guide.stl
09-charger-light-guide.stl x 2
