sayhiben/little-on-air/hardware/enclosure/output/v216/bambu-studio/all-plates/on-air-v216-X1C-all-plates.3mf

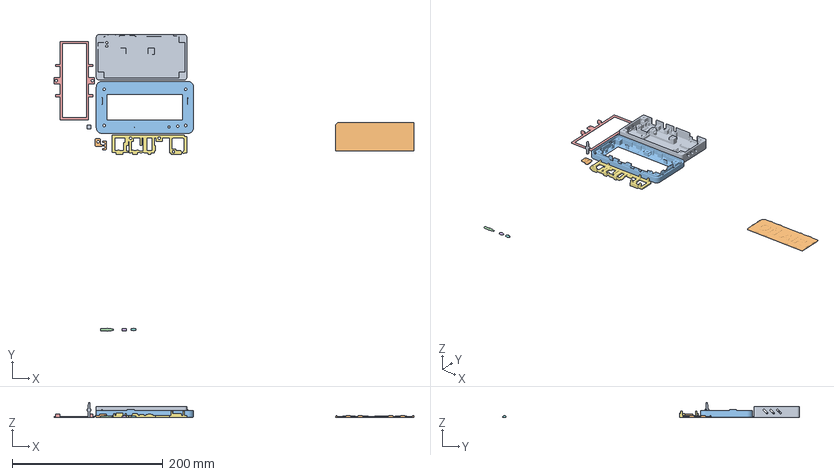
[picture p81: CAD file, 2026-09-26]
hardware/enclosure/output/v216/bambu-studio/all-plates/on-air-v216-X1C-all-plates.3mf
477.2 x 393.4 x 20.1 mm
05-rear-electronics-housing.stl
03-registered-graphic-backing.stl
01-front-optical-bezel.stl
08-captive-front-rgb-guide.stl
04-optical-retainer.stl
09-charger-light-guide.stl x 2
06-electronics-retaining-yoke.stl
07-front-guided-reset-button.stl
11-rear-light-guide-keeper.stl
