sayhiben/little-on-air/hardware/enclosure/output/v216/bambu-studio/input-upgrade-parts.3mf

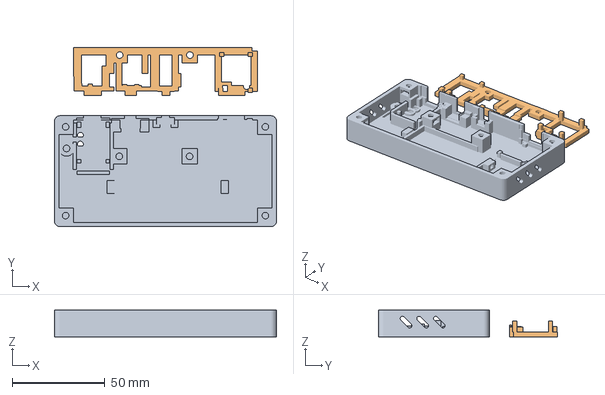
[picture p82: CAD file, 2026-09-26]
hardware/enclosure/output/v216/bambu-studio/input-upgrade-parts.3mf
120.0 x 97.0 x 14.5 mm
05-rear-electronics-housing.stl
06-electronics-retaining-yoke.stl
