sayhiben/little-on-air/hardware/enclosure/output/v216/meshes-assembly-coordinates/05-rear-electronics-housing.stl

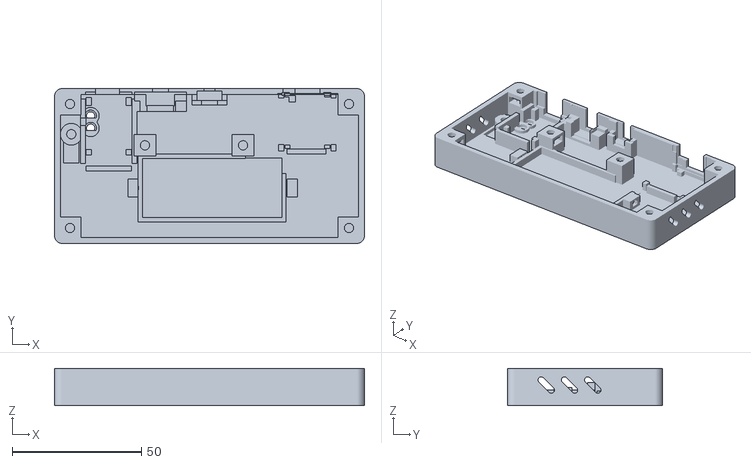
[picture p83: CAD file, 2026-09-26]
hardware/enclosure/output/v216/meshes-assembly-coordinates/05-rear-electronics-housing.stl
120.0 x 60.0 x 14.5
