sayhiben/little-on-air/hardware/enclosure/output/v216/obstacles/00.stl

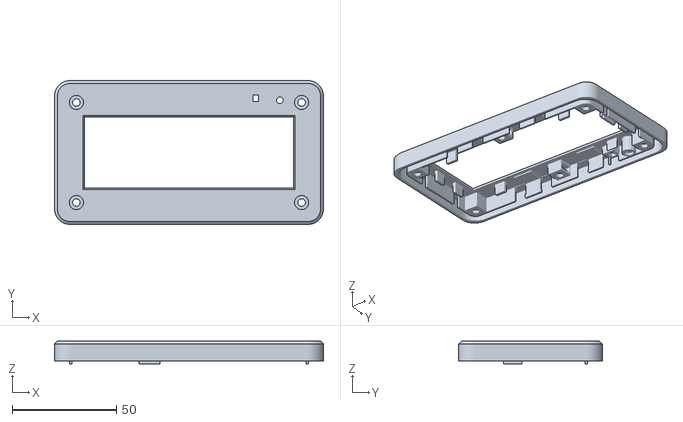
[picture p84: CAD file, 2026-09-26]
hardware/enclosure/output/v216/obstacles/00.stl
129.0 x 69.0 x 11.0
