sayhiben/little-on-air/hardware/enclosure/output/v28-light-pipes/meshes-assembly-coordinates/09-charger-2.95mm.stl

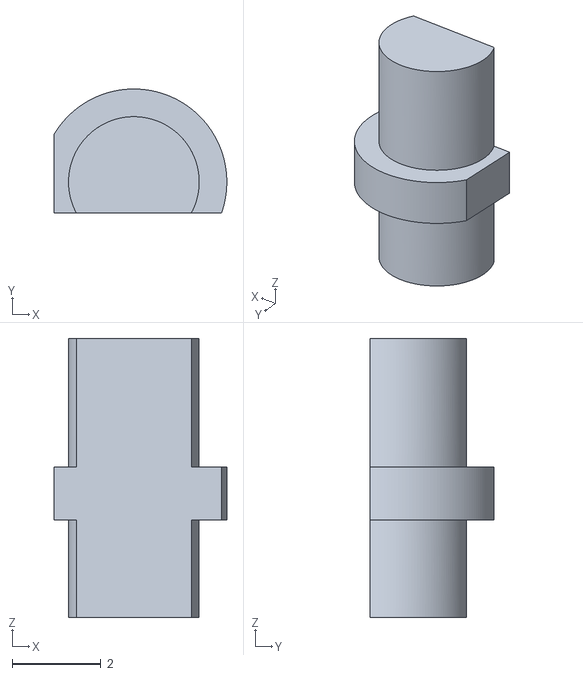
[picture p85: CAD file, 2026-09-26]
hardware/enclosure/output/v28-light-pipes/meshes-assembly-coordinates/09-charger-2.95mm.stl
3.90 x 2.80 x 6.30
