sayhiben/little-on-air/hardware/enclosure/output/v28-light-pipes/stl/09-charger-3.15mm.stl

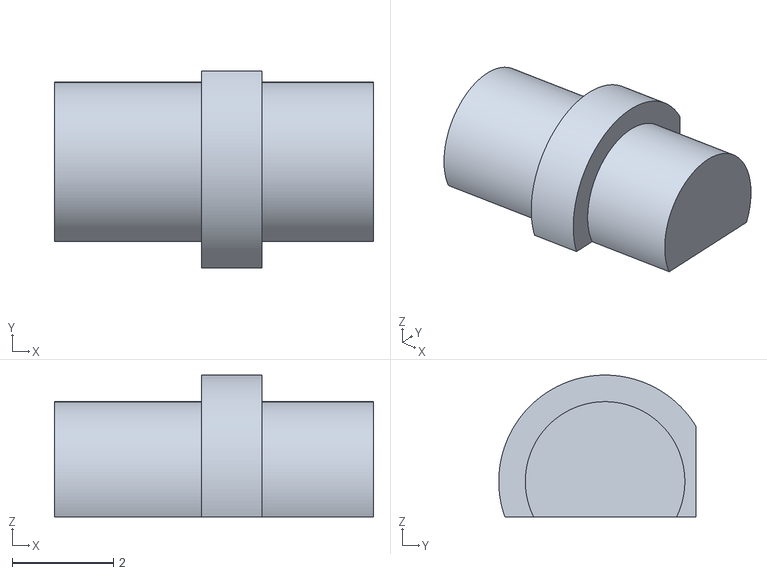
[picture p86: CAD file, 2026-09-26]
hardware/enclosure/output/v28-light-pipes/stl/09-charger-3.15mm.stl
6.30 x 3.90 x 2.80
