sayhiben/little-on-air/release/little-on-air-enclosure-v2.16/alternatives/laminate/81-laminate-front-spacer.stl

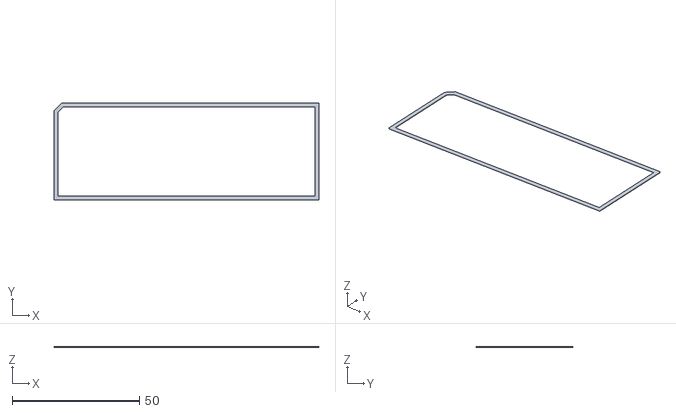
[picture p87: CAD file, 2026-09-26]
release/little-on-air-enclosure-v2.16/alternatives/laminate/81-laminate-front-spacer.stl
104.0 x 38.0 x 0.5
