sayhiben/little-on-air/hardware/controller/igor-desk-v1/output/assembly-meshes/xiao-reference.stl

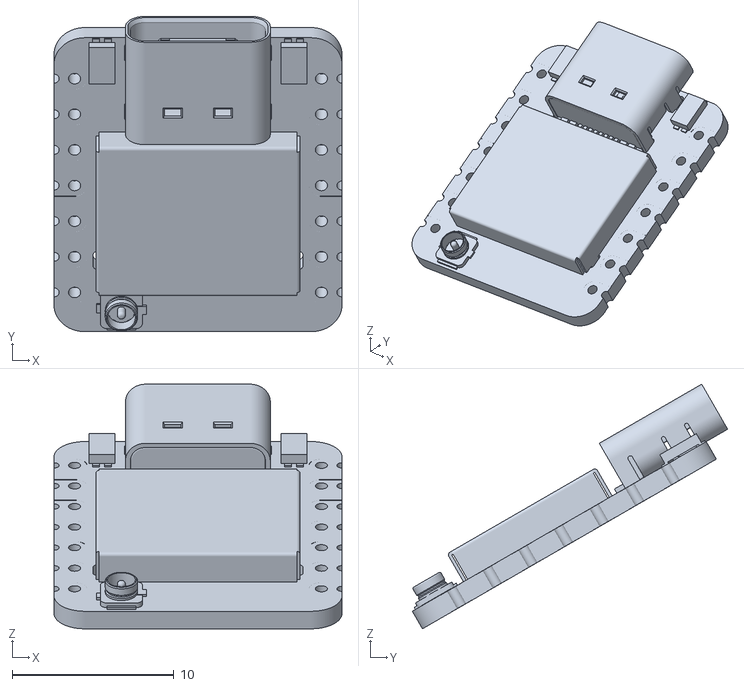
[picture p88: CAD file, 2026-09-26]
hardware/controller/igor-desk-v1/output/assembly-meshes/xiao-reference.stl
17.8 x 19.5 x 15.1
