sayhiben/little-on-air/hardware/controller/igor-desk-v1/output/bambu-studio/igor-desk-v1-X1C-clear-PETG-diffuser.3mf

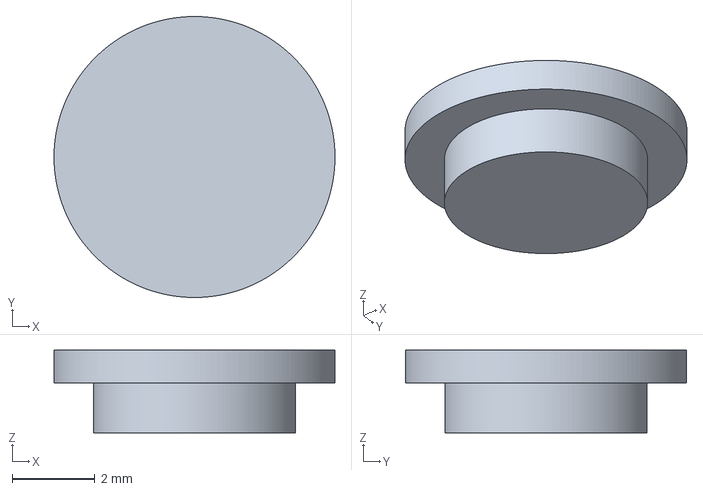
[picture p89: CAD file, 2026-09-26]
hardware/controller/igor-desk-v1/output/bambu-studio/igor-desk-v1-X1C-clear-PETG-diffuser.3mf
6.80 x 6.80 x 2.00 mm
