sayhiben/little-on-air/hardware/controller/igor-flat-base-v3/output/assembly-meshes/03-igor-hat-original.stl

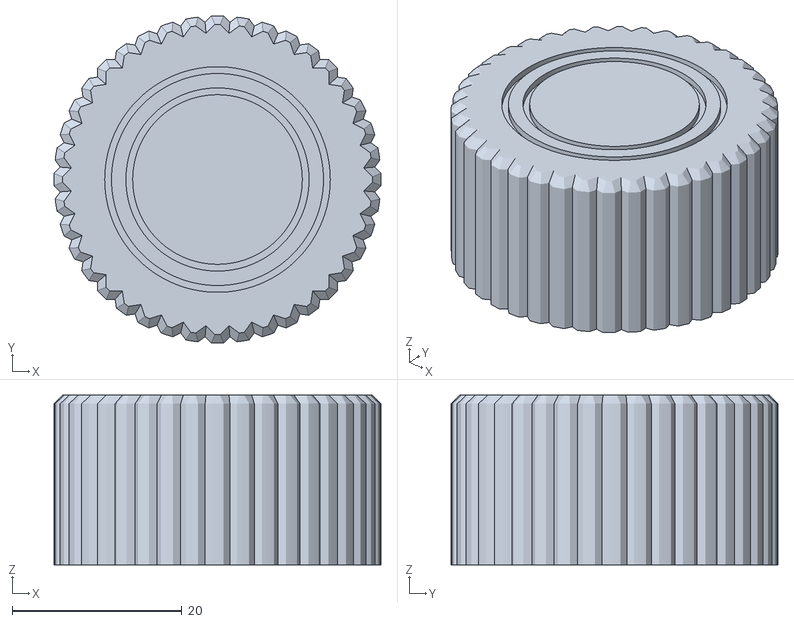
[picture p90: CAD file, 2026-09-26]
hardware/controller/igor-flat-base-v3/output/assembly-meshes/03-igor-hat-original.stl
38.6 x 38.6 x 20.0
