sayhiben/little-on-air/hardware/controller/igor-flat-base-v3/output/bambu-studio/igor-flat-base-v3-X1C-PLA-face-inlays.3mf

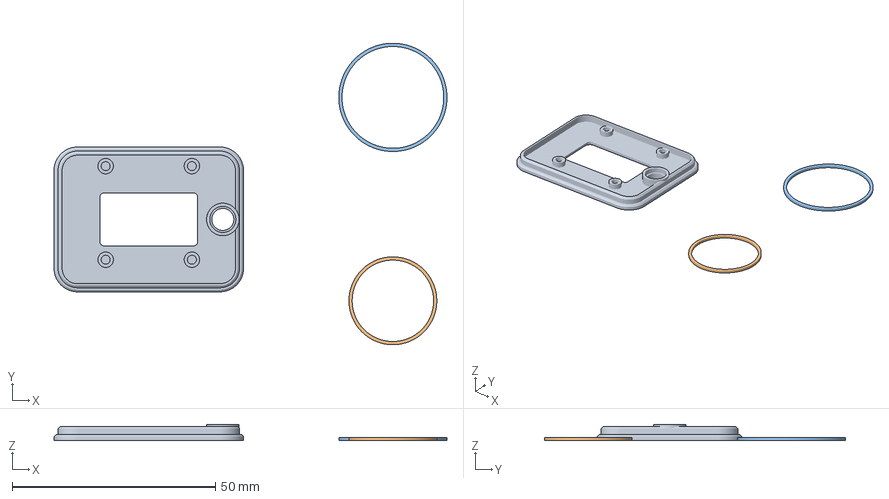
[picture p91: CAD file, 2026-09-26]
hardware/controller/igor-flat-base-v3/output/bambu-studio/igor-flat-base-v3-X1C-PLA-face-inlays.3mf
96.6 x 74.1 x 4.00 mm
02-igor-front-led-faceplate.stl
04-igor-small-inlay-original.stl
05-igor-large-inlay-original.stl
