sayhiben/little-on-air/hardware/controller/igor-flat-base-v3/output/cad/igor-flat-base-v3.step

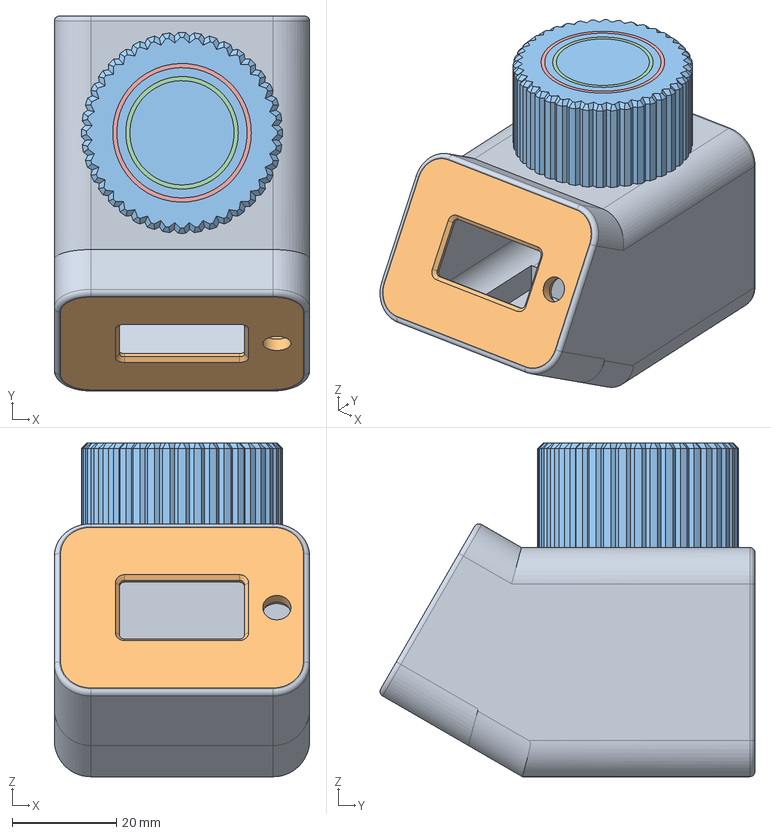
[picture p92: CAD file, 2026-09-26]
hardware/controller/igor-flat-base-v3/output/cad/igor-flat-base-v3.step
49.0 x 72.0 x 64.0 mm
01-igor-flat-base-shell
02-igor-front-led-faceplate
03-igor-hat-original
04-igor-small-inlay-original
05-igor-large-inlay-original
