sayhiben/little-on-air/hardware/controller/igor-measured-v4/output/assembly-meshes/04-igor-small-inlay-original.stl

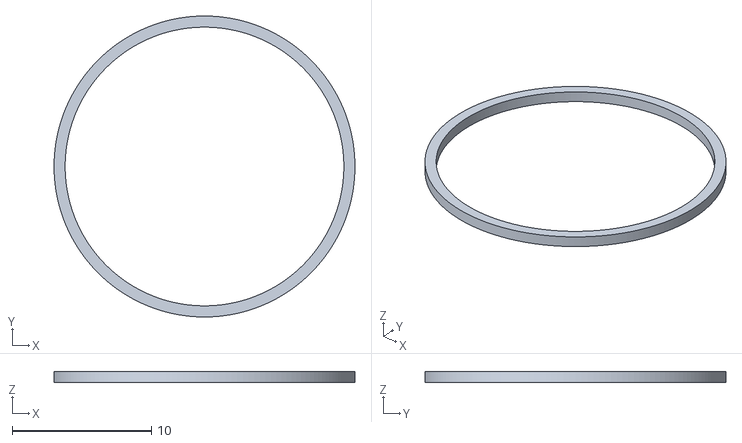
[picture p93: CAD file, 2026-09-26]
hardware/controller/igor-measured-v4/output/assembly-meshes/04-igor-small-inlay-original.stl
21.6 x 21.6 x 0.8
