sayhiben/little-on-air/hardware/controller/igor-measured-v4/output/bambu-studio/igor-measured-v4-X1C-transparent-PETG-diffuser.3mf

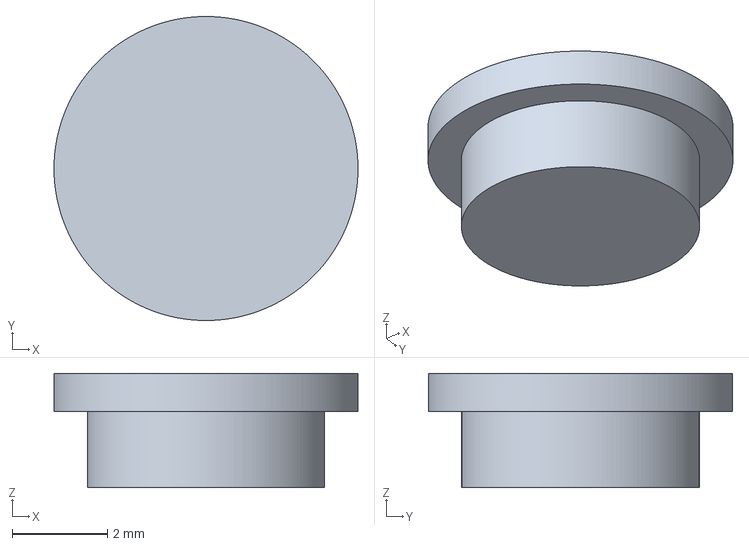
[picture p94: CAD file, 2026-09-26]
hardware/controller/igor-measured-v4/output/bambu-studio/igor-measured-v4-X1C-transparent-PETG-diffuser.3mf
6.40 x 6.40 x 2.40 mm
