sayhiben/little-on-air/hardware/controller/igor-measured-v4/output/cad/07-strip-cassette.step

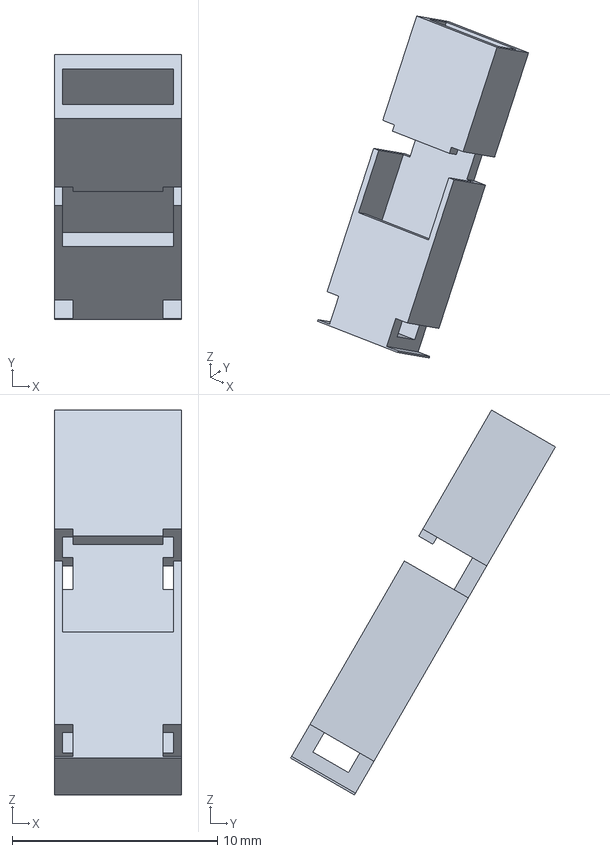
[picture p95: CAD file, 2026-09-26]
hardware/controller/igor-measured-v4/output/cad/07-strip-cassette.step
6.20 x 12.9 x 18.8 mm
