sayhiben/little-on-air/hardware/controller/igor-measured-v4/output/reference-components/oled-glass.step

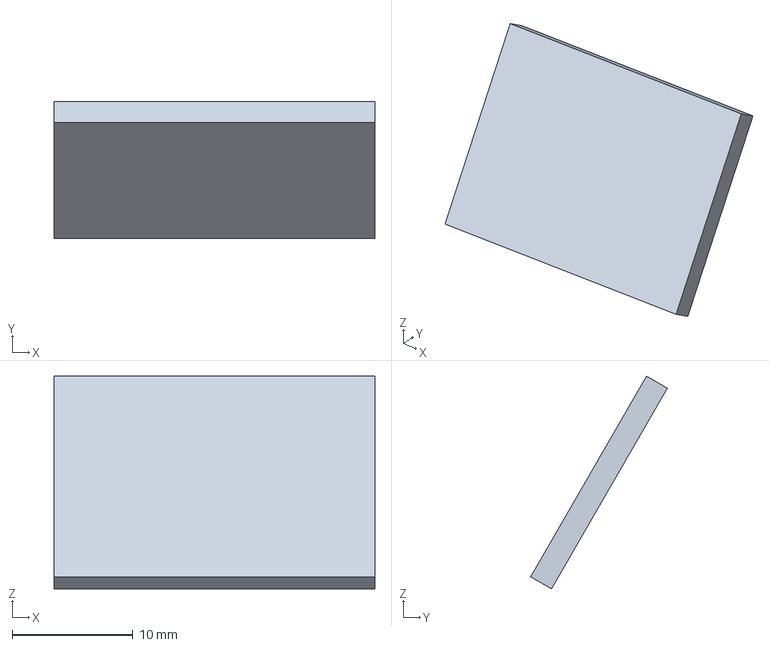
[picture p96: CAD file, 2026-09-26]
hardware/controller/igor-measured-v4/output/reference-components/oled-glass.step
26.6 x 11.3 x 17.6 mm
