sayhiben/little-on-air/hardware/controller/igor-minimal-v2/output/assembly-meshes/04-igor-small-inlay-original.stl

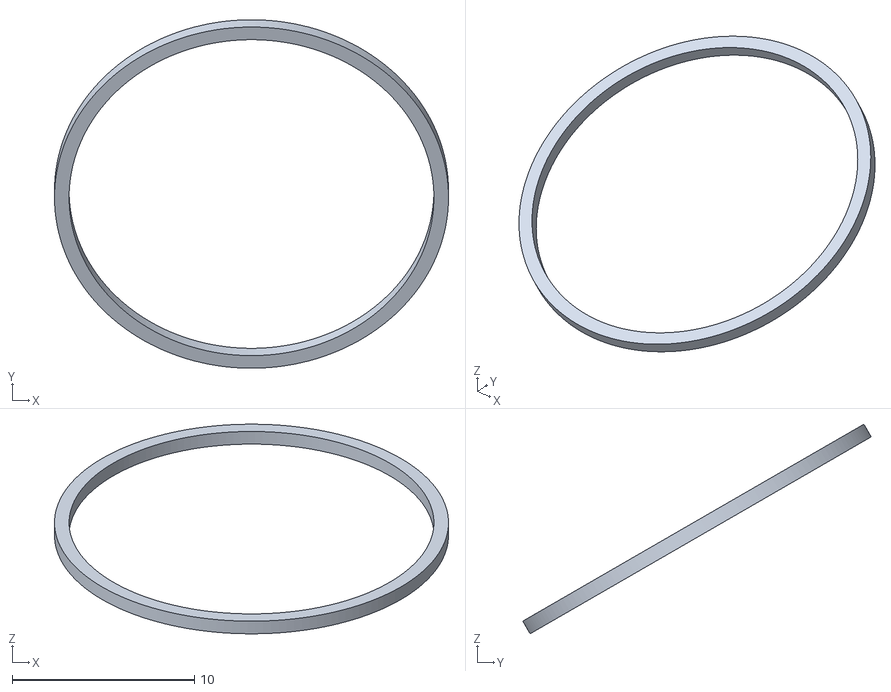
[picture p97: CAD file, 2026-09-26]
hardware/controller/igor-minimal-v2/output/assembly-meshes/04-igor-small-inlay-original.stl
21.6 x 19.1 x 11.5
