sayhiben/little-on-air/hardware/controller/igor-minimal-v2/output/bambu-studio/igor-minimal-v2-X1C-PLA-shell-hat.3mf

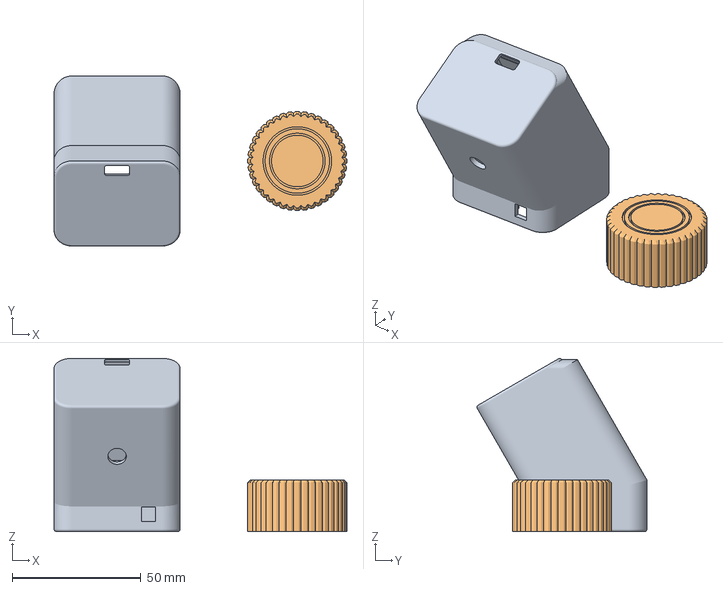
[picture p98: CAD file, 2026-09-26]
hardware/controller/igor-minimal-v2/output/bambu-studio/igor-minimal-v2-X1C-PLA-shell-hat.3mf
113.8 x 66.0 x 67.3 mm
01-igor-shell-minimal.stl
03-igor-hat-original.stl
