sayhiben/little-on-air/hardware/enclosure/output/design-review/references/bottom.dxf

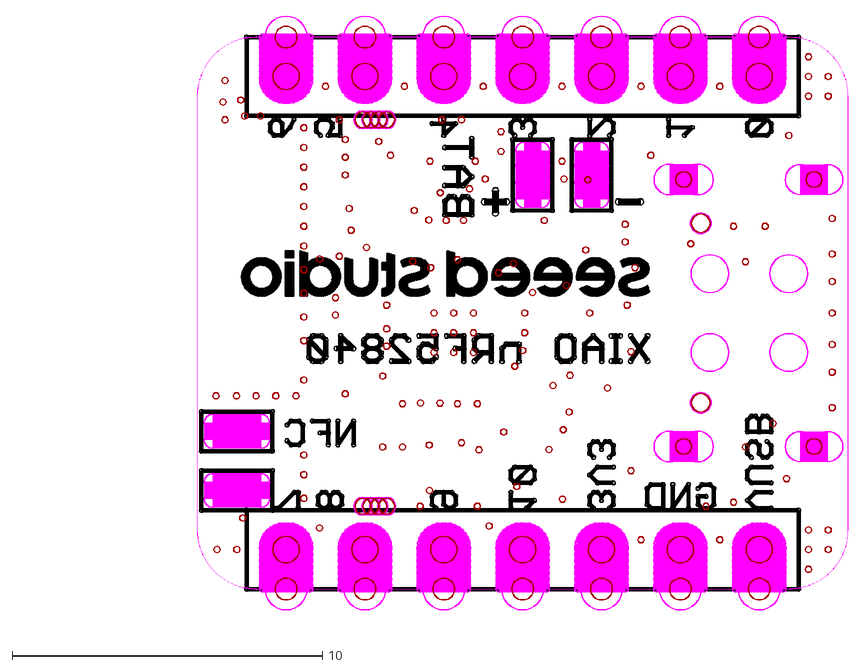
[picture p99: CAD file, 2026-09-26]
hardware/enclosure/output/design-review/references/bottom.dxf
26.8 x 19.7
