sayhiben/little-on-air/hardware/enclosure/output/fdm-and-acrylic/fit-samples/92-reset-guide-fit-sample.stl

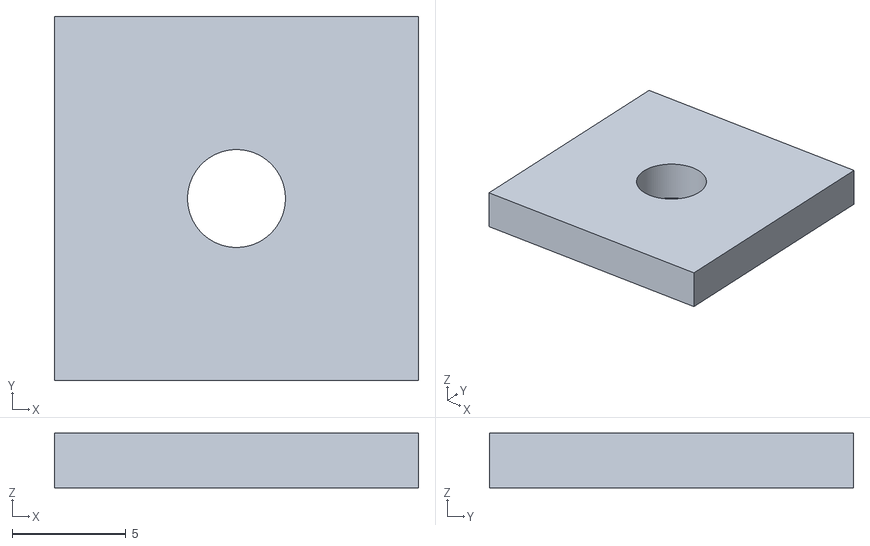
[picture p100: CAD file, 2026-09-26]
hardware/enclosure/output/fdm-and-acrylic/fit-samples/92-reset-guide-fit-sample.stl
16.0 x 16.0 x 2.40
