sayhiben/little-on-air/hardware/enclosure/output/fdm-and-acrylic/stl/10-wall-back-plate.stl

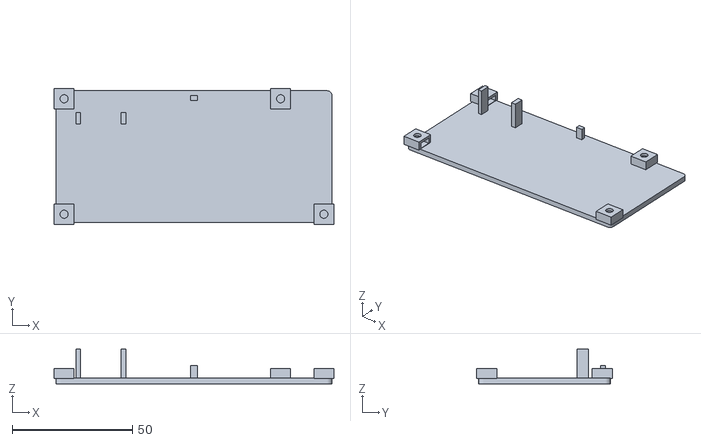
[picture p101: CAD file, 2026-09-26]
hardware/enclosure/output/fdm-and-acrylic/stl/10-wall-back-plate.stl
116.4 x 56.4 x 14.4
