sayhiben/little-on-air/hardware/enclosure/output/laser/acrylic-rear-face.dxf

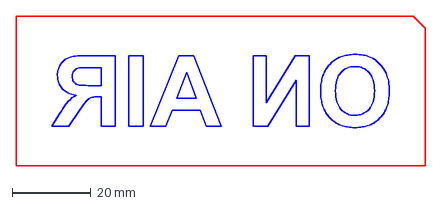
[picture p102: CAD file, 2026-09-26]
hardware/enclosure/output/laser/acrylic-rear-face.dxf
104.0 x 38.0 mm
