sayhiben/little-on-air/hardware/enclosure/output/meshes-assembly-coordinates/91-led-and-acrylic-fit-sample.stl

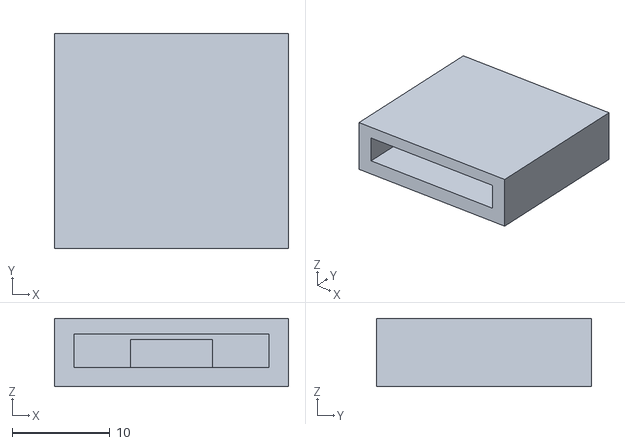
[picture p103: CAD file, 2026-09-26]
hardware/enclosure/output/meshes-assembly-coordinates/91-led-and-acrylic-fit-sample.stl
24.0 x 22.0 x 7.00
