sayhiben/little-on-air/hardware/enclosure/output/on-air-v213-captive-light-guides/bambu-studio/on-air-v213-X1C-PETG-retention-housings.3mf

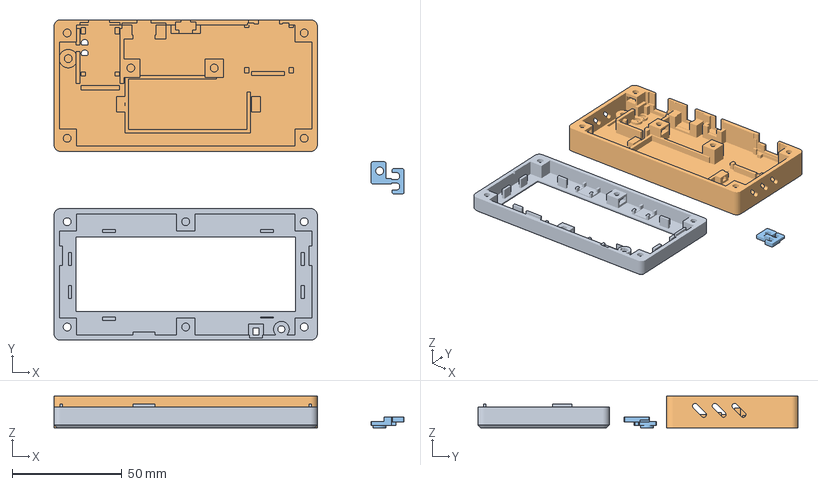
[picture p104: CAD file, 2026-09-26]
hardware/enclosure/output/on-air-v213-captive-light-guides/bambu-studio/on-air-v213-X1C-PETG-retention-housings.3mf
159.5 x 146.0 x 14.5 mm
01-front-optical-bezel.stl
05-rear-electronics-housing.stl
11-rear-light-guide-keeper.stl
