sayhiben/little-on-air/hardware/enclosure/output/on-air-v28-fabrication/fit-samples/91-upper-front-fastener-fit-section.stl

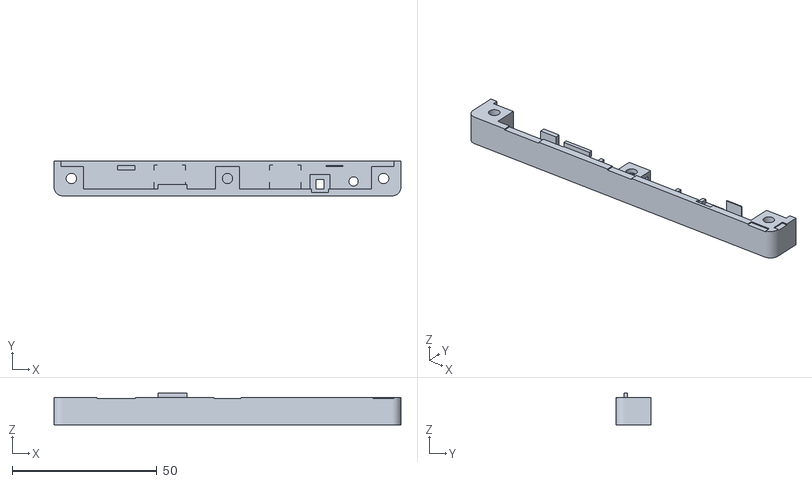
[picture p105: CAD file, 2026-09-26]
hardware/enclosure/output/on-air-v28-fabrication/fit-samples/91-upper-front-fastener-fit-section.stl
120.0 x 12.0 x 11.0
