sayhiben/little-on-air/hardware/enclosure/output/on-air-v28-fabrication/stl/04-optical-retainer.stl

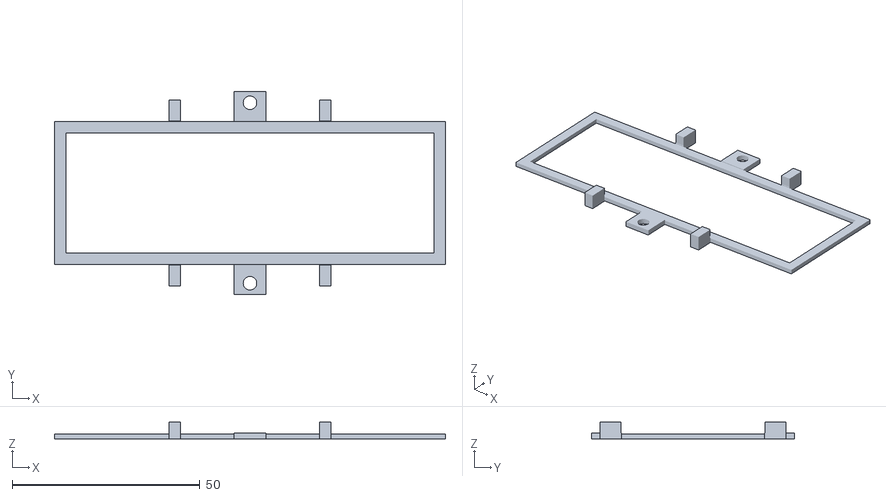
[picture p106: CAD file, 2026-09-26]
hardware/enclosure/output/on-air-v28-fabrication/stl/04-optical-retainer.stl
104.0 x 54.0 x 4.47
