sayhiben/little-on-air/hardware/enclosure/output/on-air-v28-light-pipes/stl/08-front-rgb-2.95mm.stl

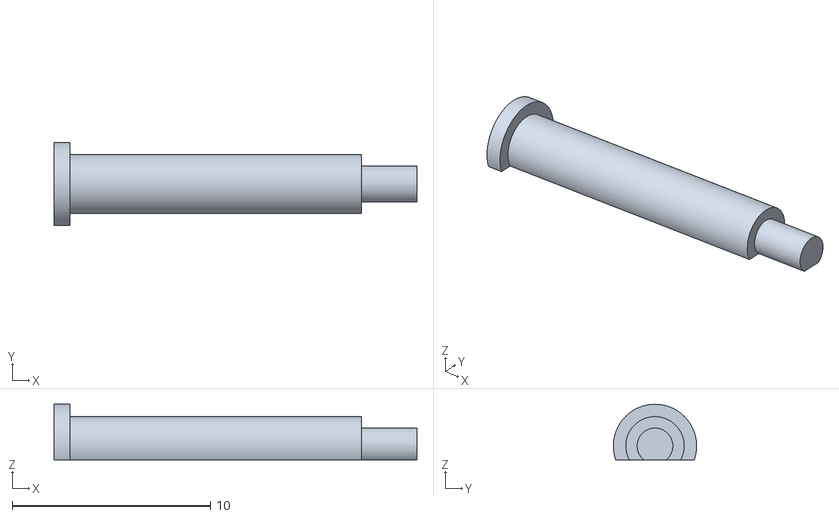
[picture p107: CAD file, 2026-09-26]
hardware/enclosure/output/on-air-v28-light-pipes/stl/08-front-rgb-2.95mm.stl
18.3 x 4.20 x 2.80
