sayhiben/little-on-air/hardware/enclosure/output/v216/meshes-assembly-coordinates/06-electronics-retaining-yoke.stl

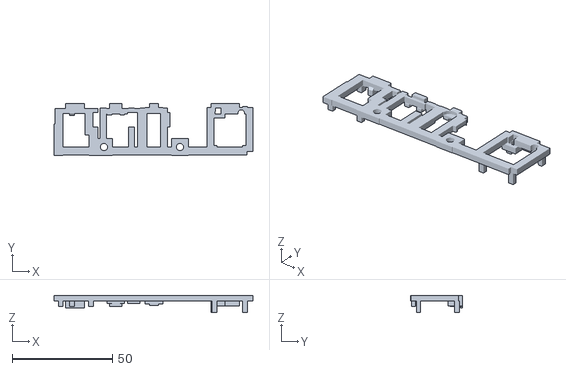
[picture p108: CAD file, 2026-09-26]
hardware/enclosure/output/v216/meshes-assembly-coordinates/06-electronics-retaining-yoke.stl
99.4 x 26.0 x 8.60
