sayhiben/little-on-air/hardware/enclosure/output/v216/obstacles/21.stl

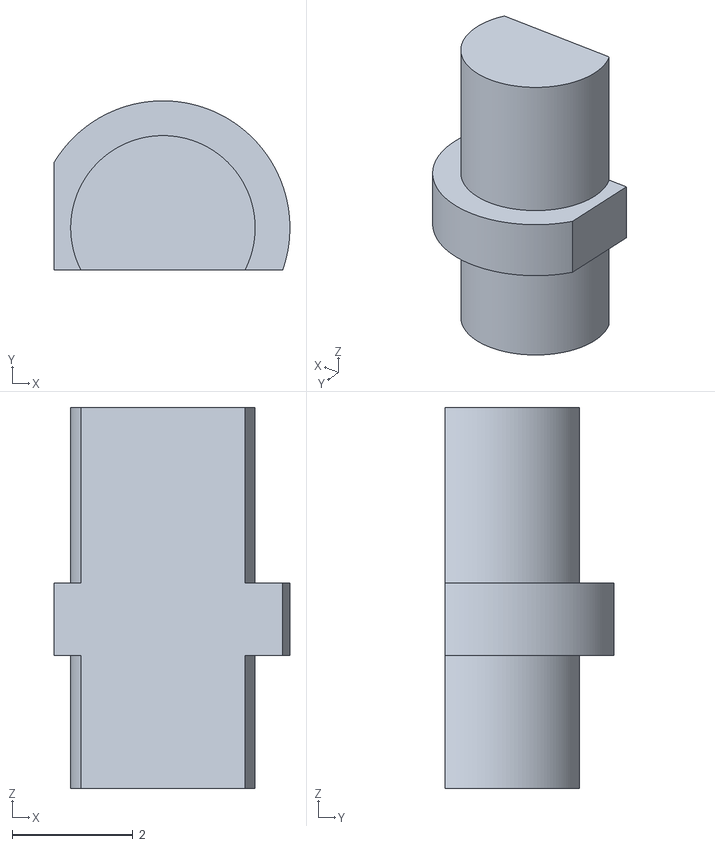
[picture p109: CAD file, 2026-09-26]
hardware/enclosure/output/v216/obstacles/21.stl
3.90 x 2.80 x 6.30
