sayhiben/little-on-air/hardware/controller/igor-desk-v1/output/bambu-studio/igor-desk-v1-X1C-PLA-body.3mf

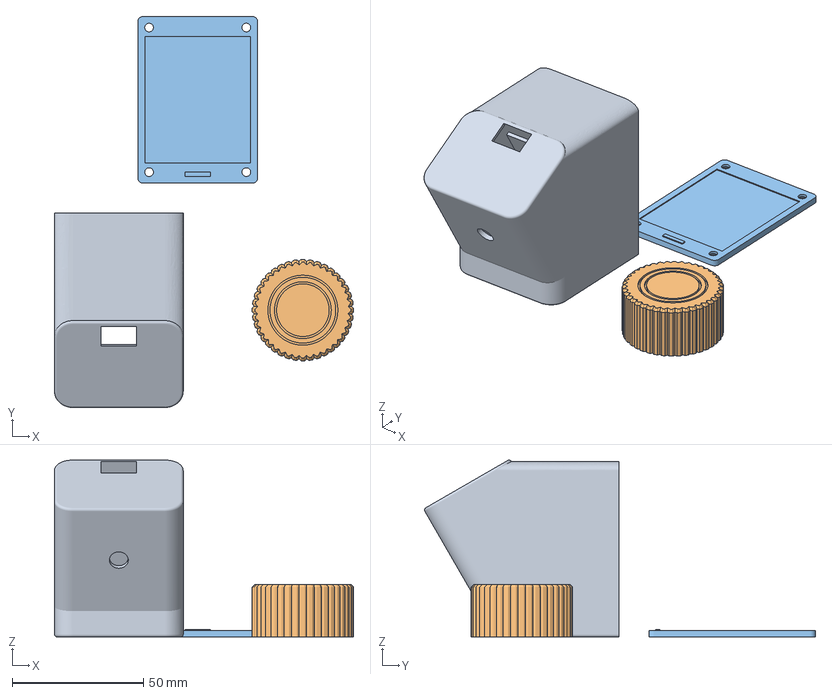
[picture p110: CAD file, 2026-09-26]
hardware/controller/igor-desk-v1/output/bambu-studio/igor-desk-v1-X1C-PLA-body.3mf
113.8 x 148.7 x 67.3 mm
01-weighted-shell.stl
03-igor-hat.stl
04-ballast-cover.stl
