sayhiben/little-on-air/hardware/controller/igor-flat-base-v3/output/assembly-meshes/02-igor-front-led-faceplate.stl

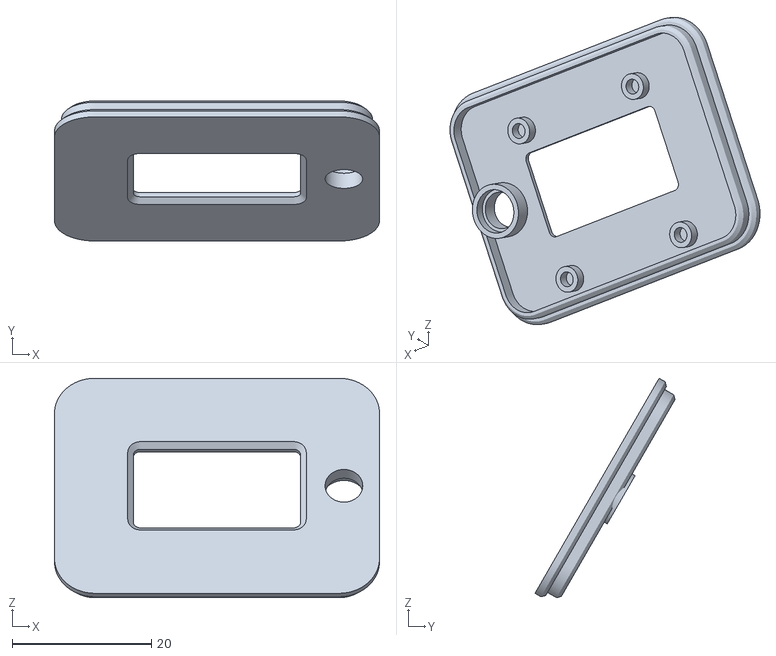
[picture p111: CAD file, 2026-09-26]
hardware/controller/igor-flat-base-v3/output/assembly-meshes/02-igor-front-led-faceplate.stl
46.6 x 20.1 x 31.5
