sayhiben/little-on-air/hardware/controller/igor-flat-base-v3/output/cad/01-igor-flat-base-shell.step

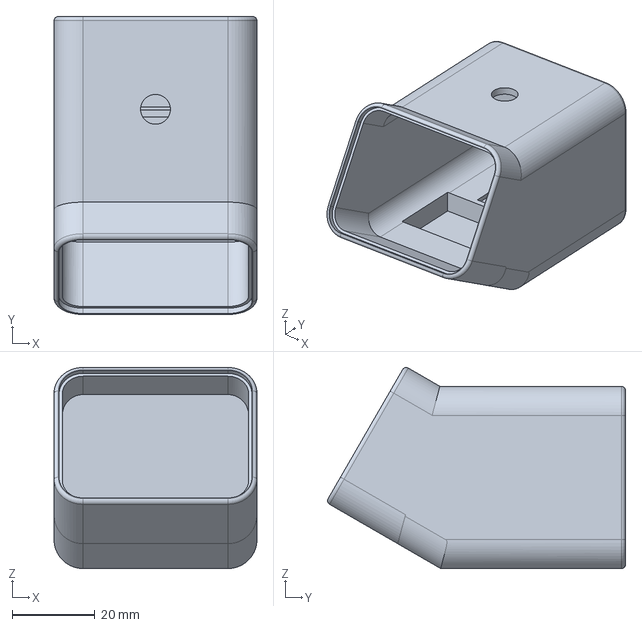
[picture p112: CAD file, 2026-09-26]
hardware/controller/igor-flat-base-v3/output/cad/01-igor-flat-base-shell.step
49.0 x 72.0 x 48.5 mm
