sayhiben/little-on-air/hardware/controller/igor-measured-v4/output/bambu-studio/igor-measured-v4-X1C-PLA-shell-hat-carrier.3mf

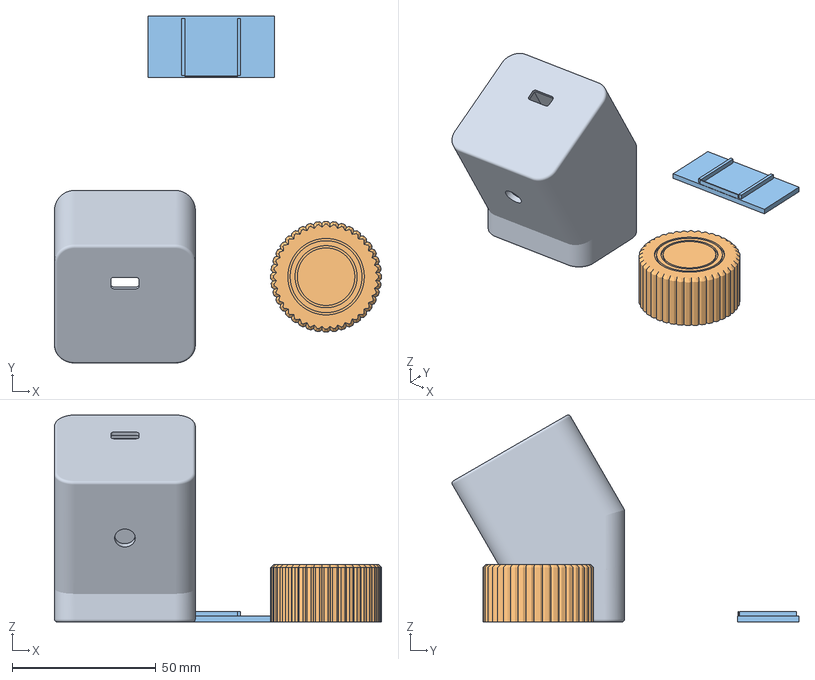
[picture p113: CAD file, 2026-09-26]
hardware/controller/igor-measured-v4/output/bambu-studio/igor-measured-v4-X1C-PLA-shell-hat-carrier.3mf
113.8 x 120.7 x 72.0 mm
01-igor-measured-shell.stl
03-igor-measured-hat.stl
08-xiao-carrier.stl
