sayhiben/little-on-air/hardware/controller/igor-minimal-v2/output/cad/03-igor-hat-original.step

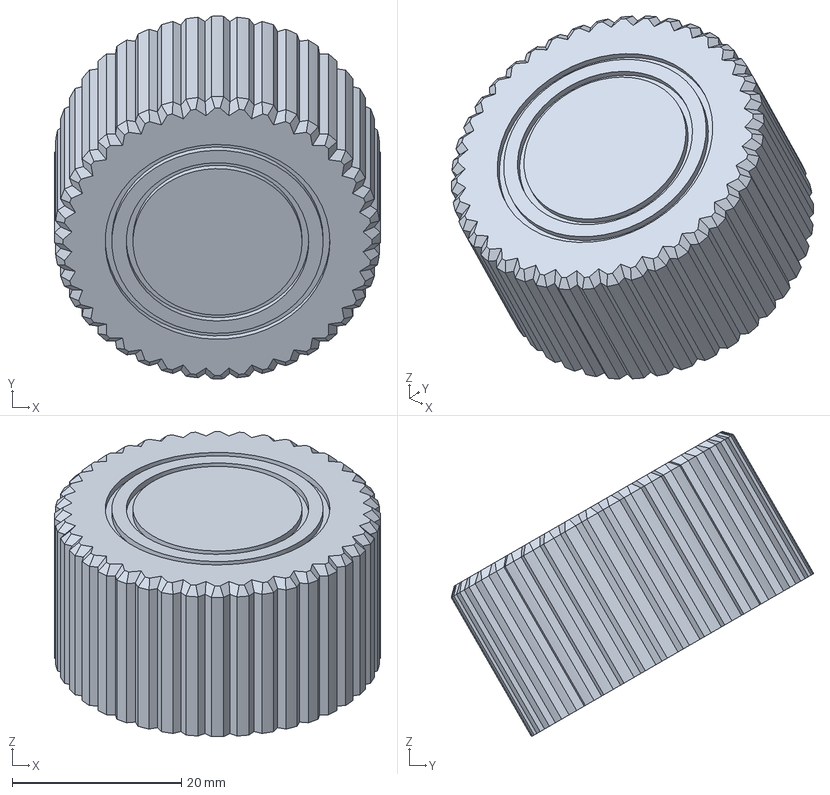
[picture p114: CAD file, 2026-09-26]
hardware/controller/igor-minimal-v2/output/cad/03-igor-hat-original.step
38.6 x 42.9 x 36.1 mm
