sayhiben/little-on-air/hardware/enclosure/output/on-air-v28-fabrication/fit-samples/96-optical-retainer-section.stl

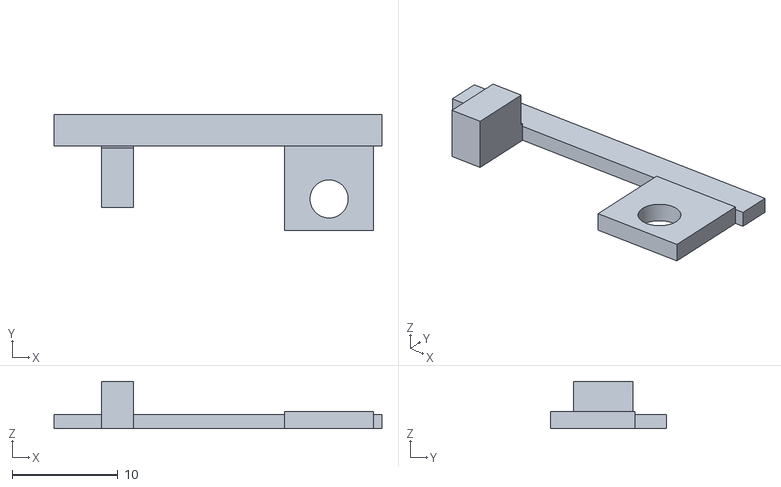
[picture p116: CAD file, 2026-09-26]
hardware/enclosure/output/on-air-v28-fabrication/fit-samples/96-optical-retainer-section.stl
31.0 x 11.0 x 4.47
