sayhiben/little-on-air/hardware/enclosure/output/on-air-v28-fabrication/START-HERE.md

# ON AIR v2.8 — two replacement parts

Open **bambu-studio/on-air-v28-X1C-eSUN-PLA-plus-fit-checks.3mf** as a complete project. It contains revised upper rear sample 99 and reset button 07. Reuse your v2.7 upper front sample 91 and keeper 06. Generic PLA and PETG projects are included too.

The packaged eSUN PLA+ fit project was opened and sliced in Bambu Studio: **1 h 22 min / 22.40 g**, including preparation. It is ready in Preview; no print was sent.

The charger stop is now the full 17.5 mm board width. The reset collar is 0.20 mm shorter, adding 0.20 mm of travel without changing the tip's rest position or guide fit.

After testing both charger corner contact and a light reset click with full release, print full **05 rear housing**. Retain the tested new **07 button** and reuse the other v2.7 parts. Full production projects are also supplied for a fresh build.

`REVISION-NOTES.md` explains the changes. `BUILD-AND-ASSEMBLY.md` includes the revised test and retained wiring/laser instructions. `stl/` contains oriented millimetre meshes; `cad/` contains native Fusion and STEP files. `laser/` contains the unchanged acrylic files, including the already mirrored rear-engraving master. `validation/` contains the checks and their limits.

Body: 120 × 60 × 24 mm; 26.5 mm including the unpressed front button. Eight M3×8 button-head screws and ordinary M3 nuts. No electrical or optical changes.

The button uses 0.10 mm layers and automatic support. First-layer inspection remains disabled and bed leveling enabled. No print or laser job has been sent.
