sayhiben/little-on-air/hardware/archive/enclosure/output/on-air-v23-fabrication/START-HERE.md

# ON AIR v2.3

Start with **bambu-studio/on-air-v23-X1C-eSUN-PLA-plus-fit-checks.3mf**. This is the measured-fit revision based on the physical v2.2 test. Replace parts 05, 06 and 07 together; omit printed part 08. Read REVISION-NOTES.md, then BUILD-AND-ASSEMBLY.md.

The laser artwork and front optical parts remain unchanged. First-layer inspection is disabled in the new Bambu projects. Retain embedded project settings, keep bed leveling enabled, and watch the first two layers manually.

Full-material projects and the separate STLs are provided after the fit check. The CAD archive remains editable in Fusion. Actual physical acceptance of these revised fits is still pending your next print.
