sayhiben/little-on-air/hardware/archive/enclosure/output/on-air-v24-fabrication/START-HERE.md

# ON AIR v2.4

Start with **bambu-studio/on-air-v24-X1C-eSUN-PLA-plus-fit-checks.3mf**: one continuous upper housing sample, yoke and reset button. Use the two M3x8 yoke screws and nuts for a representative test.

Read REVISION-NOTES.md and BUILD-AND-ASSEMBLY.md. Install the button first; insert the XIAO 8 mm low and slide it upward before fitting the yoke. Replace production parts 05, 06 and 07 together after this fit test passes.

First-layer inspection remains disabled; bed leveling remains available. The housing and yoke profiles use no automatic support. Only the small button uses support. Keep the supplied orientations and watch the first layers.

The acrylic SVGs and front optical parts remain unchanged. Actual acceptance of the new fits requires the next print.
