sayhiben/little-on-air/hardware/controller/igor-desk-v1/output/views/assembled.png

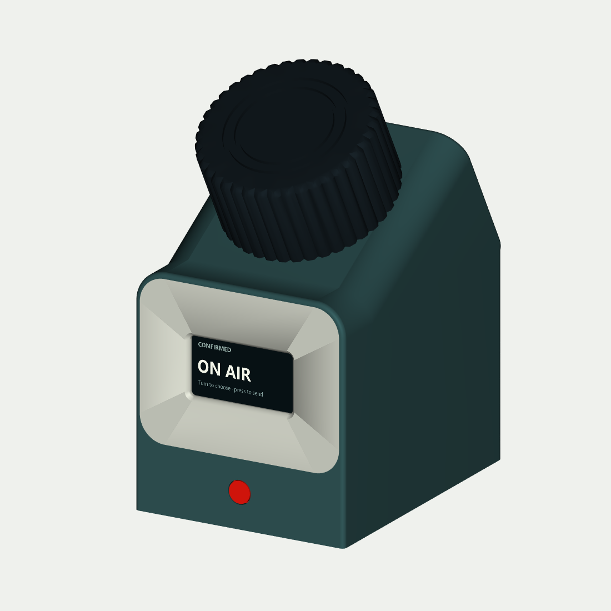
hardware/controller/igor-desk-v1/output/views/assembled.png
