sayhiben/little-on-air/hardware/controller/igor-desk-v1/output/views/print-plate.png

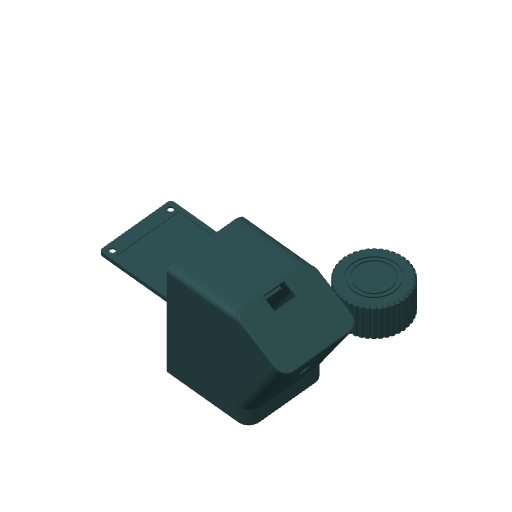
hardware/controller/igor-desk-v1/output/views/print-plate.png
