sayhiben/little-on-air/hardware/controller/igor-flat-base-v3/output/views/print-plate.png

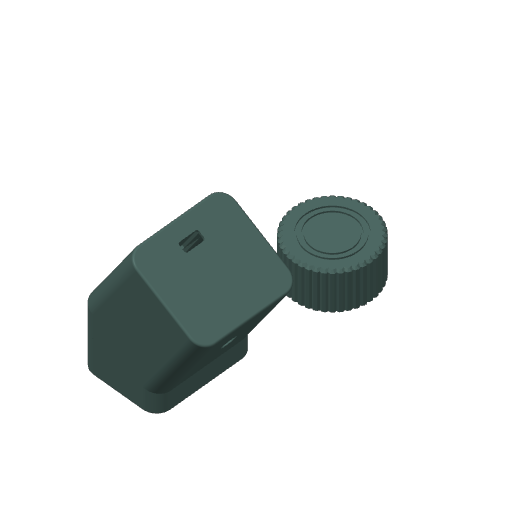
hardware/controller/igor-flat-base-v3/output/views/print-plate.png
