sayhiben/little-on-air/hardware/controller/igor-measured-v4/output/views/print-plate.png

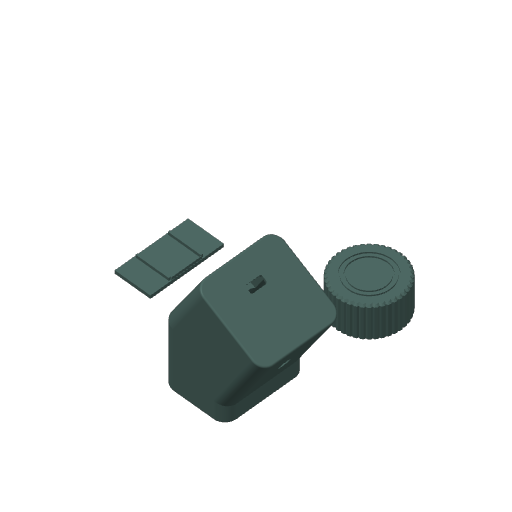
hardware/controller/igor-measured-v4/output/views/print-plate.png
