sayhiben/little-on-air/hardware/enclosure/output/on-air-v28-fabrication/views/front-reset-and-indicator.png

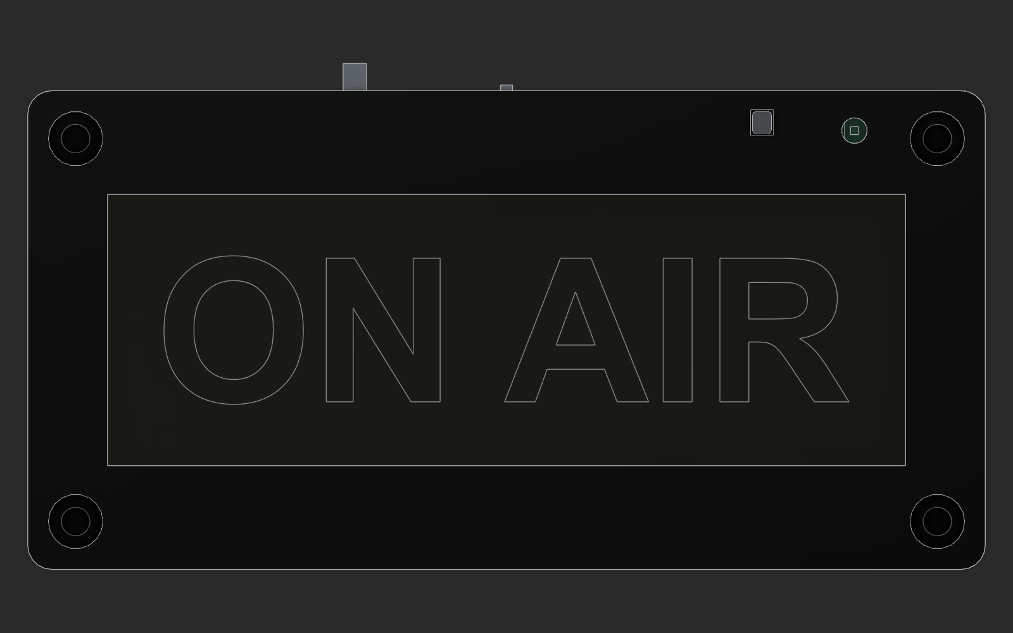
hardware/enclosure/output/on-air-v28-fabrication/views/front-reset-and-indicator.png
