sayhiben/little-on-air/hardware/enclosure/output/on-air-v28-fabrication/views/parallel-boards-layout.png

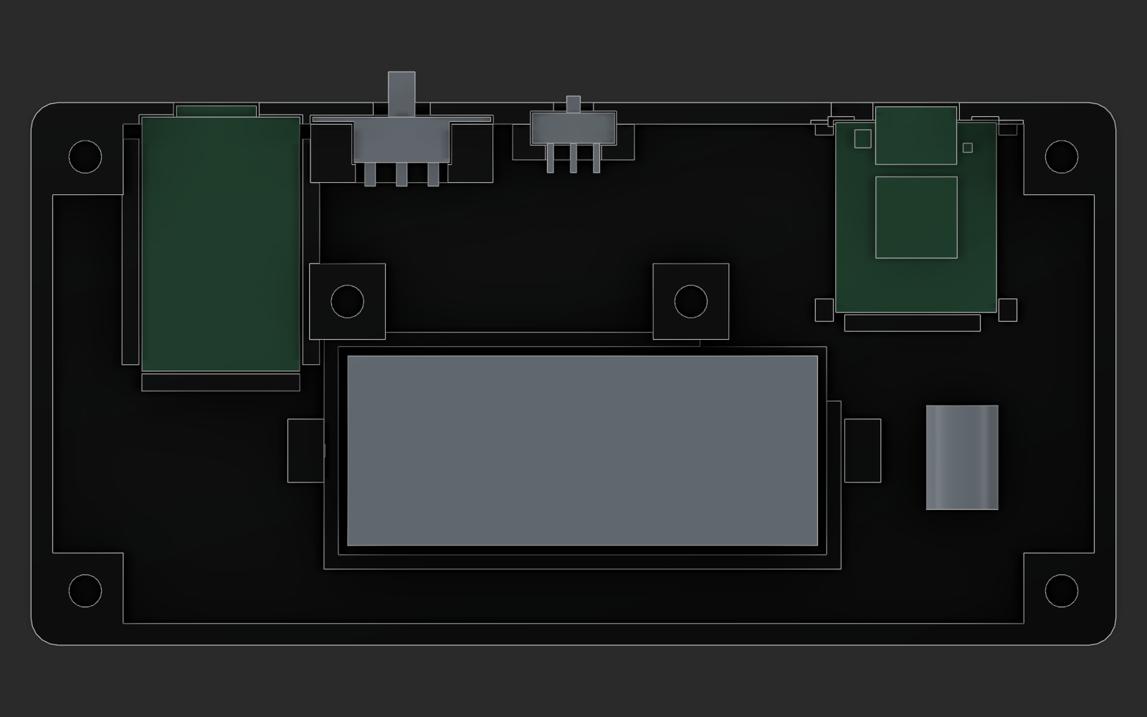
hardware/enclosure/output/on-air-v28-fabrication/views/parallel-boards-layout.png
