sayhiben/little-on-air/hardware/enclosure/output/on-air-v28-fabrication/views/side-profile.png

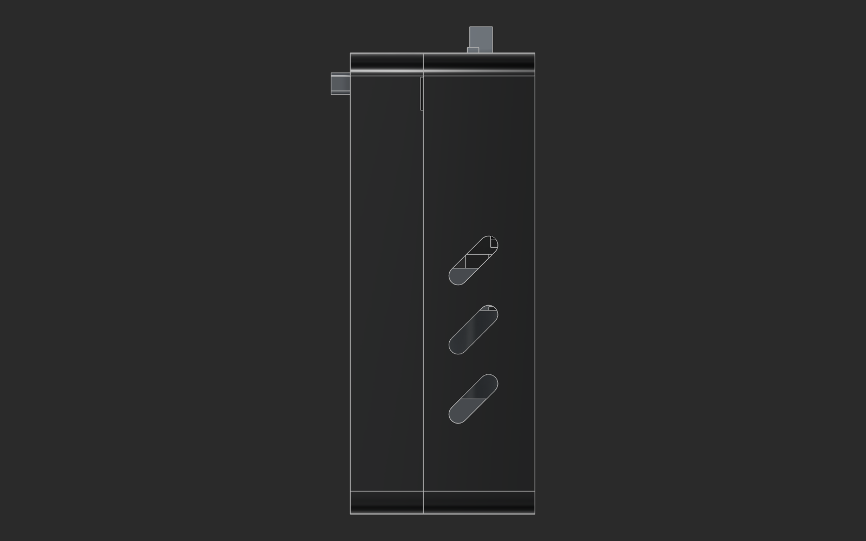
hardware/enclosure/output/on-air-v28-fabrication/views/side-profile.png
