sayhiben/little-on-air/hardware/enclosure/output/on-air-v28-light-pipes/views/front-guide-shape.png

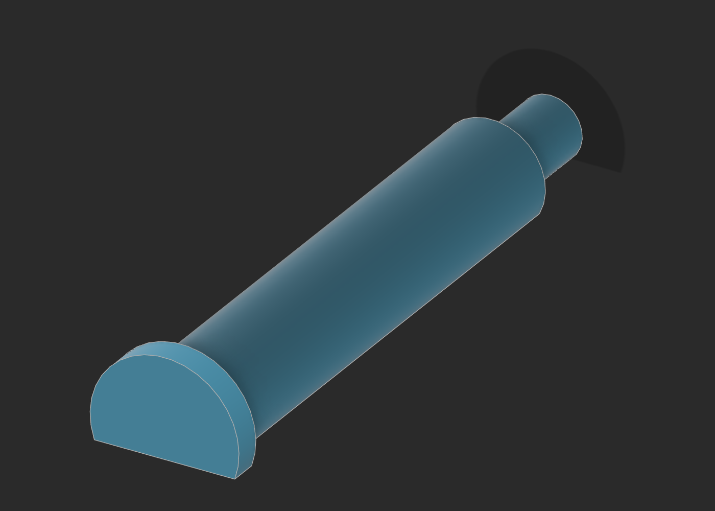
hardware/enclosure/output/on-air-v28-light-pipes/views/front-guide-shape.png
