sayhiben/little-on-air/hardware/enclosure/output/on-air-v28-light-pipes/views/separate-charger-guides.png

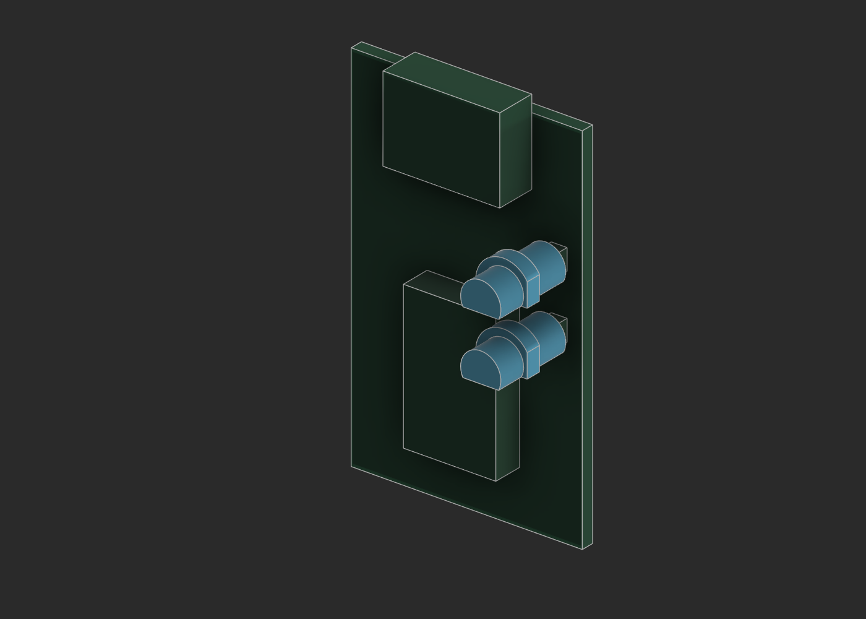
hardware/enclosure/output/on-air-v28-light-pipes/views/separate-charger-guides.png
