sayhiben/little-on-air/hardware/enclosure/output/on-air-v210-beveled-front/views/beveled-assembly.png

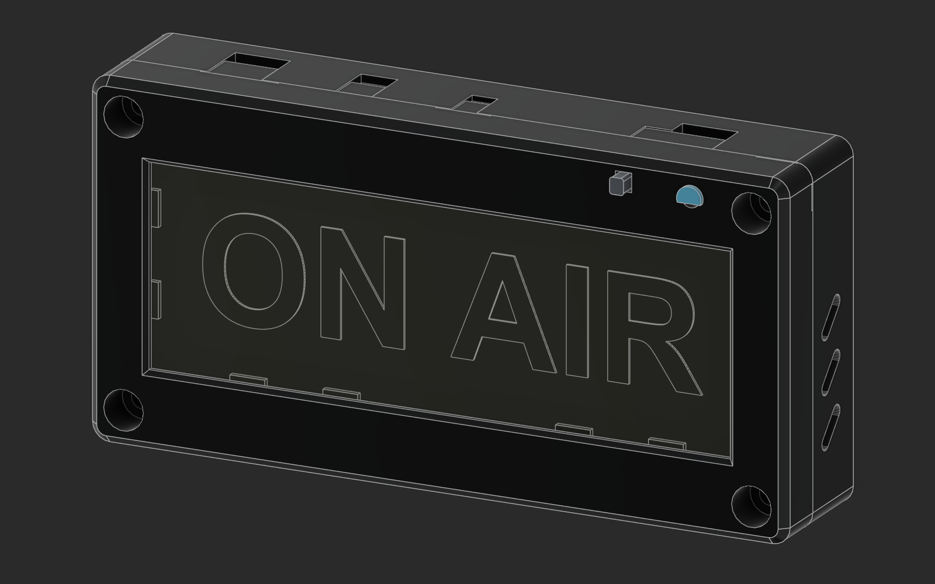
hardware/enclosure/output/on-air-v210-beveled-front/views/beveled-assembly.png
