sayhiben/little-on-air/hardware/enclosure/output/on-air-v213-captive-light-guides/views/front-captive-guide.png

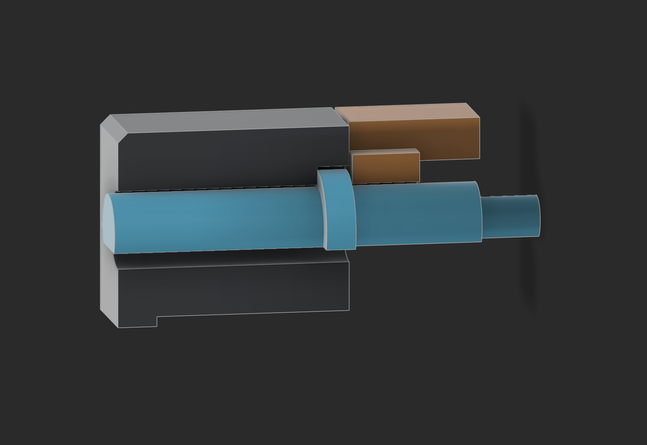
hardware/enclosure/output/on-air-v213-captive-light-guides/views/front-captive-guide.png
