sayhiben/little-on-air/release/little-on-air-enclosure-v2.16/reference/views/v214-assembly.png

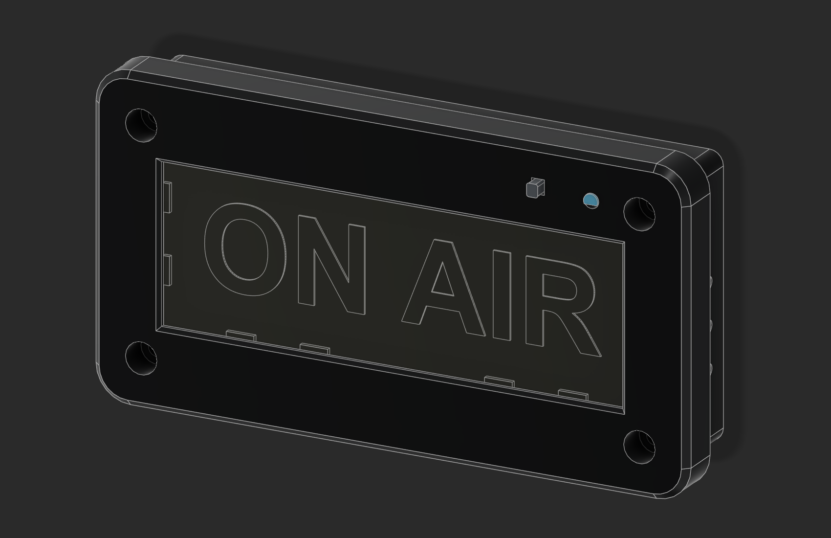
release/little-on-air-enclosure-v2.16/reference/views/v214-assembly.png
