sayhiben/little-on-air/hardware/archive/enclosure/output/on-air-v26-fabrication/VALIDATION.md

# v2.6 validation

- All 16 assembly/control paths passed, with no unhealthy features or native solid interference.
- All eight nut loading paths and common M3×8 screw engagement stacks checked.
- Both complete DPDT terminal rows and the enlarged USB keepout checked.
- Reset has 0.10 mm nominal free play and 0.40 mm total stroke.
- Fourteen XIAO edge-pad exits, two underside power-pad exits and three indicator sight lines checked.
- Reserved wire corridors and solder bays checked against the final components and hardware; all 78 route pairs checked for packing.
- Eighteen watertight meshes, each a connected solid with a defined print-bed face.
- Nine Bambu projects sliced and compared against exported STL geometry.
- The eSUN PLA+ fit project opened, sliced and saved in Bambu Studio; its estimate is recorded in the GUI validation report.
- First-layer inspection commands absent; bed leveling, intended pauses and heater shutdown checked.
- Native archive reimport preserves volumes and remains free of interference.
- Laser files match v2.5 byte for byte.

The fabrication package is produced only after these checks pass. Physical fit, strength, electronics behavior and laser material settings remain subject to the build checks. No fabrication or firmware flashing was started.
