sayhiben/little-on-air/hardware/archive/enclosure/output/on-air-v23-fabrication/VALIDATION.md

# v2.3 validation

- 15 sampled assembly/control paths passed.
- No native solid interferences or unhealthy timeline features.
- 41 wire and solder-space checks passed.
- 17 exported meshes are watertight, single connected solids and oriented on the bed.
- 9 Bambu projects sliced and their embedded meshes matched the STLs.
- The eSUN PLA+ fit project also opened and sliced in the Bambu GUI; its saved copy retained the intended meshes, material settings and inspection-off setting.
- All first-layer scan commands are absent from the new sliced projects.
- Laser file hashes match v2.2 byte for byte.

Physical fits remain subject to the measured-part coupon tests. No printer, laser or firmware operation was started.
