sayhiben/little-on-air/hardware/archive/enclosure/output/on-air-v24-fabrication/VALIDATION.md

# v2.4 validation

- 16 sampled assembly and control paths passed.
- No native solid interference or unhealthy timeline features.
- 41 wire and solder-space checks passed; all route pairs checked for simultaneous wire packing.
- The enlarged XIAO USB interior envelope clears the seated parts and the specified insertion sequence.
- 18 meshes are watertight, single connected solids and placed on the print bed.
- Nine Bambu projects sliced and their meshes match the exported STLs.
- The eSUN PLA+ fit project opened, sliced and saved in the Bambu GUI; the saved copy preserves meshes, material settings and the inspection workaround. Its displayed estimate is 2 h 22 min / 39.10 g.
- First-layer inspection commands are absent; bed leveling, expected pauses and heater shutdown checked.
- Laser files match v2.3 byte for byte.

Physical fit and strength remain subject to the next combined fit sample. No physical fabrication was started.
