sayhiben/little-on-air/hardware/archive/enclosure/output/on-air-v22-fabrication/COMMISSIONING.csv

Check | Acceptance or instruction | Measured result | Pass/date
Printer / spool | X1C 0.4; calibrated flow/pressure advance; actual PLA/PLA+/PETG spool
Surface tolerance / seam | Critical surfaces within +/-0.10 mm; seam closes by hand; no wire pinch
All eight nuts and screws | Nuts enter freely; heads and screw tips inset; correct lengths
S1 drawing vs actual | Body10.5x5.5x5.7; flange19.5; lever envelope <=3.2; measure travel
S1 sample98 and yoke | Both detents clear aperture and roof; captive; no flange/terminal clash
S2 sample94 and slider | Both detents; 1.42 square fork fit; nominal2.58 movement
Reset and both switches | 20 operations each; no sticking or moving wires
Both USBs | Real cable overmolds fit and latch; PCBs stay seated
LED segments | Entire cut outline and SMD components fit; emitting edges face acrylic
Pigtails / cap / resistor | Actual bodies and insulated bends fit reserved space without load on pouch
Acrylic material and thickness | Confirmed PMMA; measure5points;3.00-3.45; calculate rear cushion
Laser RF setup | Record lens/focus/air; verified Nova Plus24 60W RF device
Kerf | Record plug/opening X/Y at top/bottom; compensate outline only
Engraving | Record RF speed/min-max power/interval/passes; frosted shallow fill
Acrylic registration | Already mirrored SVG; common datums; practical text mismatch <=0.15 mm aim
Switch continuity before battery | S1 common and throws; both independent S2 poles; NC throws insulated
POWER off | Charger stays on cell; main load rail disconnected from charger OUT+
PROGRAM isolation | XIAO BAT+ and DATA each isolated from switched LED rail/harness
USB modes | POWER off + PROGRAM before either USB; only selected port plugged
Cell rating / protection | Obtain cell max charge current; verify charger setting and protection
Charge test | Load disconnected; measured charge current <=cell rating; termination and temperature pass
Switch currents | S1 steady load below0.5A and startup checked; S2 MCU branch including startup below100mA
External firmware | Four external pixels supported; correct order and brightness ceiling
Lighting across battery range | Start at12.5% ceiling; verify colors, no flicker/reset as battery discharges
Closed case | Intended run and charge tests; target <=40C cell/case at20-25C ambient or cell-maker lower limit
Final mounting | No internal movement; connector service slack; flat rear and adequate wall strips
