sayhiben/little-on-air/hardware/controller/igor-measured-v4/output/views/cutaway.png

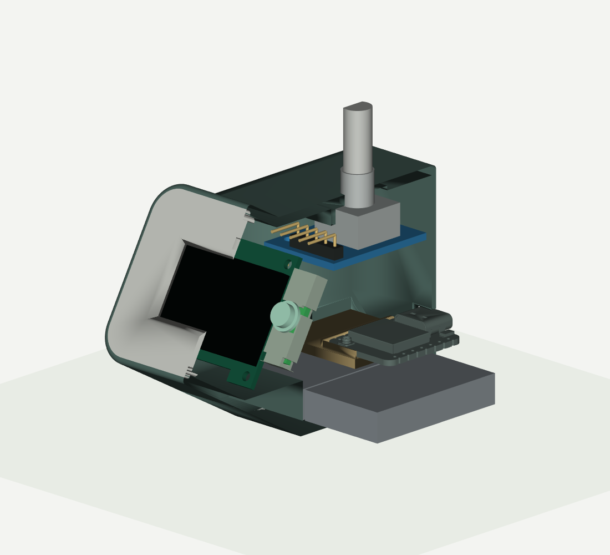
hardware/controller/igor-measured-v4/output/views/cutaway.png
