sayhiben/little-on-air/hardware/controller/igor-measured-v4/output/views/diffuser-detail-raw.png

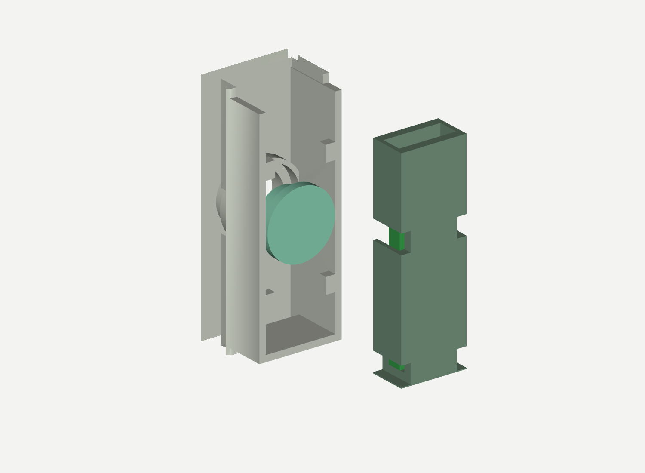
hardware/controller/igor-measured-v4/output/views/diffuser-detail-raw.png
