sayhiben/little-on-air/release/little-on-air-enclosure-v2.13/RELEASE-NOTES.md

# Current release contents

This consolidates the v2.13 frame, rear housing and captive guides with the unchanged v2.8 backing, optical retainer, electronics yoke and corrected reset button. The complete editable Fusion/STEP assembly is v2.13. Laser artwork and the optional laminate stack are unchanged.

The Bambu project retains the user's three-plate arrangement and painted insert. It restores black/white PLA+ and clear optical PETG profiles, and removes the user-identified spare guide keeper. The original edited file is preserved outside the release. All three plates were re-sliced and verified.

Documentation now gives one current assembly order, nine matching screws/nuts, direct DPDT actuation, full-width charger stop, corrected reset stroke, front and rear guide capture, the selected capacitor/resistor-only two-switch circuit and the firmware limitation. Old fit coupons and alternate-size guide sets are excluded from production files.

The capacitor/resistor documentation update adds an illustrated soldering walkthrough, exact lead connections, polarity identification, component purposes and meter checks. The assembly guide, wiring guide, BOM and commissioning checklist point to the same connections. Fabrication files and the selected firmware snapshot are unchanged.
