sayhiben/little-on-air/release/little-on-air-enclosure-v2.14/RELEASE-NOTES.md

# Enclosure v2.14

Only front frame 01 changes: 4.5 mm wider per side, a covered 4.2 × 6.3 mm perimeter wire loop outside all four corner and both central optical-retainer bosses, inward access windows, and removed LED side lips above the original optical floors. The new rim preserves clearance for the original reset collar. All other CAD components, production STLs, acrylic SVGs and optional laminate parts are unchanged. No new fastener or electronic component is required.

Includes an updated three-plate Bambu project and a replacement-frame-only project. Part 01 has a required 45° bridge-angle override; rear housing 05 moves 9 mm in plate Y. Black/white PLA+ insert painting, clear PETG guide fills, one keeper, disabled first-layer inspection and all other part settings are retained.

The native comparisons, interference/motion checks, wire reservations, STL topology and actual sliced roof paths were reviewed. Use [FRONT-WIRING.md](guides/FRONT-WIRING.md) for assembly and the limits of those checks. Physical printing and assembly have not been performed for this revision.

The electrical circuit and included firmware v0.1.2 are unchanged. The capacitor/resistor soldering guide is included; external NeoPixel firmware remains pending. v2.13 is preserved separately.
