sayhiben/little-on-air/apps/receiver/src/ble_server.c

/* SPDX-License-Identifier: MIT */
#include <errno.h>
#include <string.h>

#include <zephyr/bluetooth/bluetooth.h>
#include <zephyr/bluetooth/conn.h>
#include <zephyr/bluetooth/gatt.h>
#include <zephyr/bluetooth/hci.h>
#include <zephyr/bluetooth/uuid.h>
#include <zephyr/kernel.h>
#include <zephyr/logging/log.h>
#include <zephyr/sys/atomic.h>

#include <little_on_air/protocol.h>
#include <little_on_air/receiver_processor.h>
#include <little_on_air/store.h>
#include <little_on_air/pairing_control.h>

#include "ble_server.h"
#include "brightness_settings.h"
#include "device_indicator.h"
#include "mood_indicator.h"
#include "pair_reset.h"
#include "status_output.h"

#if !defined(CONFIG_BT_SMP_SC_PAIR_ONLY) || defined(CONFIG_BT_SMP_SC_ONLY)
#error "Little On Air requires LE Secure Connections pairing with Just Works support"
#endif

LOG_MODULE_REGISTER(loa_receiver_ble);

#define PAIRING_WINDOW    K_SECONDS(60)
#define ADV_RESTART_DELAY K_MSEC(100)
#define ADV_RETRY_DELAY   K_MSEC(250)
#define ADV_FAST_INTERVAL 0x00a0U
#define ADV_SLOW_INTERVAL 0x0640U

static struct bt_uuid_128 service_uuid = BT_UUID_INIT_128(LOA_BT_UUID_SERVICE_VAL);
static struct bt_uuid_128 command_uuid = BT_UUID_INIT_128(LOA_BT_UUID_COMMAND_VAL);
static struct bt_uuid_128 state_uuid = BT_UUID_INIT_128(LOA_BT_UUID_STATE_VAL);

static struct loa_receiver_processor processor;
static struct bt_conn *current_conn;
static struct k_work indication_work;
static struct k_work_delayable advertising_restart_work;
static struct k_work_delayable pairing_timeout_work;
static struct bt_gatt_indicate_params indication_params;
static uint8_t state_payload[LOA_PROTOCOL_PAYLOAD_LEN];
static atomic_t indicating;
static bool indications_enabled;
static bool advertising;
static bool pairing_window_open;
static bool bonded;

static int persist_state(const struct loa_message *state, void *user_data)
{
	ARG_UNUSED(user_data);
	int err = loa_store_save_state(state);

	LOG_INF("persist transaction=0x%08x status=%u result=%d", state->transaction_id,
		state->status, err);
	return err;
}

static int apply_state(const struct loa_message *state, void *user_data)
{
	ARG_UNUSED(user_data);
	LOG_INF("apply transaction=0x%08x status=%u", state->transaction_id, state->status);
	if (loa_status_output_test_active()) {
		(void)loa_status_output_test_pixel(UINT8_MAX, (struct loa_rgb){0});
	}
	loa_mood_indicator_set(state->status);
	return 0;
}

static void indication_destroy(struct bt_gatt_indicate_params *params)
{
	ARG_UNUSED(params);
	LOG_DBG("indication parameters released");
	atomic_clear(&indicating);
}

static void indication_complete(struct bt_conn *conn, struct bt_gatt_indicate_params *params,
				uint8_t err)
{
	ARG_UNUSED(conn);
	ARG_UNUSED(params);
	LOG_INF("indication complete att_err=0x%02x", err);
}

static void send_indication(struct k_work *work);

static int acknowledge_state(const struct loa_message *state, void *user_data)
{
	ARG_UNUSED(user_data);
	int err = loa_protocol_encode(state_payload, state);

	if (err == 0) {
		LOG_INF("queue indication transaction=0x%08x status=%u", state->transaction_id,
			state->status);
		k_work_submit(&indication_work);
	} else {
		LOG_ERR("indication encode failed err=%d", err);
	}
	return err;
}

static ssize_t read_state(struct bt_conn *conn, const struct bt_gatt_attr *attr, void *buf,
			  uint16_t len, uint16_t offset)
{
	uint8_t payload[LOA_PROTOCOL_PAYLOAD_LEN];

	ARG_UNUSED(attr);
	LOG_INF("state read transaction=0x%08x status=%u offset=%u len=%u",
		processor.current.transaction_id, processor.current.status, offset, len);
	if (loa_protocol_encode(payload, &processor.current) != 0) {
		return BT_GATT_ERR(BT_ATT_ERR_UNLIKELY);
	}

	return bt_gatt_attr_read(conn, attr, buf, len, offset, payload, sizeof(payload));
}

static ssize_t write_command(struct bt_conn *conn, const struct bt_gatt_attr *attr, const void *buf,
			     uint16_t len, uint16_t offset, uint8_t flags)
{
	int err;

	ARG_UNUSED(conn);
	ARG_UNUSED(attr);
	LOG_INF("command write len=%u offset=%u flags=0x%02x", len, offset, flags);
	if (offset != 0U) {
		return BT_GATT_ERR(BT_ATT_ERR_INVALID_OFFSET);
	}
	if ((flags & BT_GATT_WRITE_FLAG_PREPARE) != 0U || len != LOA_PROTOCOL_PAYLOAD_LEN) {
		return BT_GATT_ERR(BT_ATT_ERR_INVALID_ATTRIBUTE_LEN);
	}

	err = loa_receiver_process_payload(&processor, buf, len);
	LOG_INF("command process result=%d current_tx=0x%08x current_status=%u", err,
		processor.current.transaction_id, processor.current.status);
	if (err == -EINVAL) {
		return BT_GATT_ERR(BT_ATT_ERR_VALUE_NOT_ALLOWED);
	}
	if (err != 0) {
		return BT_GATT_ERR(BT_ATT_ERR_UNLIKELY);
	}

	return len;
}

static void state_ccc_changed(const struct bt_gatt_attr *attr, uint16_t value)
{
	ARG_UNUSED(attr);
	indications_enabled = value == BT_GATT_CCC_INDICATE;
	LOG_INF("CCC changed value=0x%04x indications=%u", value, indications_enabled);
}

/* Encrypted diagnostics: version, pixel index (255=end), R, G, B.
 * This characteristic leaves the six-byte status protocol and stored state alone. */
static struct bt_uuid_128 pixel_uuid =
	BT_UUID_INIT_128(BT_UUID_128_ENCODE(0x7f6c0003, 0x6b7e, 0x4c80, 0x9f2a, 0xf9b9d7e2a601));
static uint8_t pixel_payload[5] = {1, UINT8_MAX, 0, 0, 0};

static ssize_t read_pixel(struct bt_conn *conn, const struct bt_gatt_attr *attr, void *buf,
			  uint16_t len, uint16_t offset)
{
	const uint8_t idle[] = {1, UINT8_MAX, 0, 0, 0};
	const uint8_t *payload = loa_status_output_test_active() ? pixel_payload : idle;
	return bt_gatt_attr_read(conn, attr, buf, len, offset, payload, sizeof(pixel_payload));
}

static ssize_t write_pixel(struct bt_conn *conn, const struct bt_gatt_attr *attr, const void *buf,
			   uint16_t len, uint16_t offset, uint8_t flags)
{
	ARG_UNUSED(conn);
	ARG_UNUSED(attr);
	const uint8_t *data = buf;
	if (offset != 0 || (flags & BT_GATT_WRITE_FLAG_PREPARE) != 0 || len != 5) {
		return BT_GATT_ERR(BT_ATT_ERR_INVALID_ATTRIBUTE_LEN);
	}
	if (data[0] != 1 || (data[1] >= 4 && data[1] != UINT8_MAX)) {
		return BT_GATT_ERR(BT_ATT_ERR_VALUE_NOT_ALLOWED);
	}
	int err =
		loa_status_output_test_pixel(data[1], (struct loa_rgb){data[2], data[3], data[4]});
	if (err != 0) {
		return BT_GATT_ERR(BT_ATT_ERR_UNLIKELY);
	}
	memcpy(pixel_payload, data, sizeof(pixel_payload));
	LOG_INF("pixel test index=%u rgb=%u,%u,%u", data[1], data[2], data[3], data[4]);
	return len;
}

static struct bt_uuid_128 pairing_control_uuid =
	BT_UUID_INIT_128(BT_UUID_128_ENCODE(0x7f6c0004, 0x6b7e, 0x4c80, 0x9f2a, 0xf9b9d7e2a601));

static ssize_t write_pairing_control(struct bt_conn *conn, const struct bt_gatt_attr *attr,
				     const void *buf, uint16_t len, uint16_t offset, uint8_t flags)
{
	ARG_UNUSED(attr);
	if (offset != 0U || (flags & BT_GATT_WRITE_FLAG_PREPARE) != 0U ||
	    !loa_pairing_control_valid(buf, len)) {
		return BT_GATT_ERR(BT_ATT_ERR_VALUE_NOT_ALLOWED);
	}
	if (!bonded || conn != current_conn || bt_conn_get_security(conn) < BT_SECURITY_L2) {
		return BT_GATT_ERR(BT_ATT_ERR_AUTHORIZATION);
	}
	/* An ATT success response means the reset intent is durable. */
	int err = loa_pair_reset_request();
	LOG_INF("remote forget persisted=%d", err);
	return err == 0 ? len : BT_GATT_ERR(BT_ATT_ERR_UNLIKELY);
}

static struct bt_uuid_128 brightness_uuid =
	BT_UUID_INIT_128(BT_UUID_128_ENCODE(0x7f6c0005, 0x6b7e, 0x4c80, 0x9f2a, 0xf9b9d7e2a601));

static ssize_t read_brightness(struct bt_conn *conn, const struct bt_gatt_attr *attr, void *buf,
			       uint16_t len, uint16_t offset)
{
	uint8_t payload[LOA_BRIGHTNESS_PAYLOAD_LEN];
	struct loa_brightness value = loa_brightness_settings_get();
	(void)loa_brightness_encode(payload, &value);
	return bt_gatt_attr_read(conn, attr, buf, len, offset, payload, sizeof(payload));
}

static ssize_t write_brightness(struct bt_conn *conn, const struct bt_gatt_attr *attr,
				const void *buf, uint16_t len, uint16_t offset, uint8_t flags)
{
	ARG_UNUSED(attr);
	if (offset != 0U) {
		return BT_GATT_ERR(BT_ATT_ERR_INVALID_OFFSET);
	}
	if ((flags & BT_GATT_WRITE_FLAG_PREPARE) != 0U || len != LOA_BRIGHTNESS_PAYLOAD_LEN) {
		return BT_GATT_ERR(BT_ATT_ERR_INVALID_ATTRIBUTE_LEN);
	}
	if (!bonded || conn != current_conn || bt_conn_get_security(conn) < BT_SECURITY_L2) {
		return BT_GATT_ERR(BT_ATT_ERR_AUTHORIZATION);
	}
	int err = loa_brightness_settings_write(buf, len);
	if (err == -EINVAL) {
		return BT_GATT_ERR(BT_ATT_ERR_VALUE_NOT_ALLOWED);
	}
	return err == 0 ? len : BT_GATT_ERR(BT_ATT_ERR_UNLIKELY);
}

BT_GATT_SERVICE_DEFINE(
	loa_service, BT_GATT_PRIMARY_SERVICE(&service_uuid),
	BT_GATT_CHARACTERISTIC(&command_uuid.uuid, BT_GATT_CHRC_WRITE, BT_GATT_PERM_WRITE_ENCRYPT,
			       NULL, write_command, NULL),
	BT_GATT_CHARACTERISTIC(&state_uuid.uuid, BT_GATT_CHRC_READ | BT_GATT_CHRC_INDICATE,
			       BT_GATT_PERM_READ_ENCRYPT, read_state, NULL, NULL),
	BT_GATT_CCC(state_ccc_changed, BT_GATT_PERM_READ | BT_GATT_PERM_WRITE_ENCRYPT),
	BT_GATT_CHARACTERISTIC(&pixel_uuid.uuid, BT_GATT_CHRC_WRITE | BT_GATT_CHRC_READ,
			       BT_GATT_PERM_WRITE_ENCRYPT | BT_GATT_PERM_READ_ENCRYPT, read_pixel,
			       write_pixel, NULL),
	BT_GATT_CHARACTERISTIC(&pairing_control_uuid.uuid, BT_GATT_CHRC_WRITE,
			       BT_GATT_PERM_WRITE_ENCRYPT, NULL, write_pairing_control, NULL),
	BT_GATT_CHARACTERISTIC(&brightness_uuid.uuid, BT_GATT_CHRC_READ | BT_GATT_CHRC_WRITE,
			       BT_GATT_PERM_READ_ENCRYPT | BT_GATT_PERM_WRITE_ENCRYPT,
			       read_brightness, write_brightness, NULL));

static void send_indication(struct k_work *work)
{
	ARG_UNUSED(work);
	if (!indications_enabled || current_conn == NULL || !atomic_cas(&indicating, 0, 1)) {
		LOG_ERR("indication skipped enabled=%u connected=%u busy=%u", indications_enabled,
			current_conn != NULL, atomic_get(&indicating) != 0);
		return;
	}

	indication_params.attr = &loa_service.attrs[4];
	indication_params.func = indication_complete;
	indication_params.destroy = indication_destroy;
	indication_params.data = state_payload;
	indication_params.len = sizeof(state_payload);
	int err = bt_gatt_indicate(current_conn, &indication_params);

	if (err != 0) {
		LOG_ERR("indication queue failed err=%d", err);
		atomic_clear(&indicating);
	} else {
		LOG_INF("indication queued");
	}
}

static const struct bt_data advertising_data[] = {
	BT_DATA_BYTES(BT_DATA_FLAGS, BT_LE_AD_GENERAL | BT_LE_AD_NO_BREDR),
	BT_DATA_BYTES(BT_DATA_UUID128_ALL, LOA_BT_UUID_SERVICE_VAL),
};

static const struct bt_data scan_response_data[] = {
	BT_DATA(BT_DATA_NAME_COMPLETE, CONFIG_BT_DEVICE_NAME, sizeof(CONFIG_BT_DEVICE_NAME) - 1U),
};

static void bond_to_filter_list(const struct bt_bond_info *info, void *user_data)
{
	int *result = user_data;
	int err = bt_le_filter_accept_list_add(&info->addr);

	if (*result == 0 && err != 0) {
		*result = err;
	}
}

static int configure_filter_list(void)
{
	int err = bt_le_filter_accept_list_clear();

	if (err != 0) {
		LOG_ERR("filter list clear failed err=%d", err);
		return err;
	}
	bt_foreach_bond(BT_ID_DEFAULT, bond_to_filter_list, &err);
	LOG_INF("filter list configured result=%d", err);
	return err;
}

static int start_advertising(bool fast, bool filter_connections)
{
	struct bt_le_adv_param params = {
		.id = BT_ID_DEFAULT,
		.sid = 0U,
		.secondary_max_skip = 0U,
		.options = BT_LE_ADV_OPT_CONN,
		.interval_min = fast ? ADV_FAST_INTERVAL : ADV_SLOW_INTERVAL,
		.interval_max = fast ? ADV_FAST_INTERVAL : ADV_SLOW_INTERVAL,
		.peer = NULL,
	};
	int err;

	if (advertising) {
		(void)bt_le_adv_stop();
		advertising = false;
	}

	if (filter_connections) {
		err = configure_filter_list();
		if (err != 0) {
			return err;
		}
		params.options |= BT_LE_ADV_OPT_FILTER_CONN;
	}

	err = bt_le_adv_start(&params, advertising_data, ARRAY_SIZE(advertising_data),
			      scan_response_data, ARRAY_SIZE(scan_response_data));
	if (err == 0) {
		advertising = true;
	}
	LOG_INF("advertising start fast=%u filtered=%u result=%d", fast, filter_connections, err);
	return err;
}

static void restart_advertising(struct k_work *work)
{
	int err;

	ARG_UNUSED(work);

	if (current_conn != NULL) {
		LOG_INF("advertising restart skipped while connected");
		return;
	}

	if (bonded) {
		err = start_advertising(false, true);
	} else if (pairing_window_open) {
		err = start_advertising(true, false);
	} else {
		return;
	}

	/* The disconnected callback runs before Zephyr releases its final
	 * connection reference. With CONFIG_BT_MAX_CONN=1 an immediate
	 * connectable-advertising restart can therefore return -ENOMEM.
	 */
	if (err == -ENOMEM || err == -EAGAIN) {
		LOG_WRN("advertising resources busy err=%d; retrying", err);
		(void)k_work_reschedule(&advertising_restart_work, ADV_RETRY_DELAY);
	}
}

static void pairing_window_expired(struct k_work *work)
{
	ARG_UNUSED(work);
	pairing_window_open = false;
	LOG_INF("pairing window expired connected=%u bonded=%u", current_conn != NULL, bonded);
	if (current_conn != NULL) {
		return;
	}

	if (advertising) {
		(void)bt_le_adv_stop();
		advertising = false;
	}
	if (bonded) {
		loa_mood_indicator_set(processor.current.status);
		(void)start_advertising(false, true);
	} else {
		loa_device_indicator_set(LOA_DEVICE_UNPAIRED);
	}
}

static void connected(struct bt_conn *conn, uint8_t err)
{
	LOG_INF("connected err=%u", err);
	if (err != 0U) {
		return;
	}

	(void)k_work_cancel_delayable(&advertising_restart_work);
	advertising = false;
	current_conn = bt_conn_ref(conn);
	/* Bonded peers connect briefly for commands and once-per-minute reads.
	 * Transport activity must never replace the sign's actual status.
	 */
	if (!bonded) {
		loa_device_indicator_set(LOA_DEVICE_PAIRING);
	}
}

static void disconnected(struct bt_conn *conn, uint8_t reason)
{
	if (conn != current_conn) {
		return;
	}
	LOG_INF("disconnected reason=0x%02x bonded=%u pairing_window=%u", reason, bonded,
		pairing_window_open);

	bt_conn_unref(current_conn);
	current_conn = NULL;
	indications_enabled = false;
	atomic_clear(&indicating);

	if (bonded) {
		/* Preserve output and animation phase across routine disconnects. */
	} else if (pairing_window_open) {
		loa_device_indicator_set(LOA_DEVICE_PAIRING);
	} else {
		loa_device_indicator_set(LOA_DEVICE_UNPAIRED);
		return;
	}

	(void)k_work_reschedule(&advertising_restart_work, ADV_RESTART_DELAY);
}

BT_CONN_CB_DEFINE(connection_callbacks) = {
	.connected = connected,
	.disconnected = disconnected,
};

static void pairing_complete(struct bt_conn *conn, bool is_bonded)
{
	ARG_UNUSED(conn);
	LOG_INF("pairing complete bonded=%u", is_bonded);
	if (!is_bonded) {
		return;
	}

	bonded = true;
	pairing_window_open = false;
	(void)k_work_cancel_delayable(&pairing_timeout_work);
	loa_device_indicator_set(LOA_DEVICE_READY);
	loa_mood_indicator_set(processor.current.status);
}

static void pairing_failed(struct bt_conn *conn, enum bt_security_err reason)
{
	ARG_UNUSED(conn);
	LOG_ERR("pairing failed reason=%u", reason);
}

static struct bt_conn_auth_info_cb auth_info_callbacks = {
	.pairing_complete = pairing_complete,
	.pairing_failed = pairing_failed,
};

static void bond_found(const struct bt_bond_info *info, void *user_data)
{
	bool *found = user_data;

	ARG_UNUSED(info);
	*found = true;
}

bool loa_ble_server_has_bond(void)
{
	bool found = false;

	bt_foreach_bond(BT_ID_DEFAULT, bond_found, &found);
	LOG_INF("bond present=%u", found);
	return found;
}

int loa_ble_server_init(const struct loa_message *initial_state)
{
	k_work_init(&indication_work, send_indication);
	k_work_init_delayable(&advertising_restart_work, restart_advertising);
	k_work_init_delayable(&pairing_timeout_work, pairing_window_expired);
	loa_receiver_processor_init(&processor, initial_state, persist_state, apply_state,
				    acknowledge_state, NULL);
	int err = bt_conn_auth_info_cb_register(&auth_info_callbacks);

	LOG_INF("server initialized transaction=0x%08x status=%u err=%d",
		initial_state->transaction_id, initial_state->status, err);
	return err;
}

int loa_ble_server_start(bool pairing_requested)
{
	bonded = loa_ble_server_has_bond();
	LOG_INF("server start pairing_requested=%u bonded=%u", pairing_requested, bonded);
	if (bonded) {
		loa_device_indicator_set(LOA_DEVICE_READY);
		loa_mood_indicator_set(processor.current.status);
		return start_advertising(false, true);
	}

	if (!pairing_requested) {
		loa_device_indicator_set(LOA_DEVICE_UNPAIRED);
		return 0;
	}

	pairing_window_open = true;
	loa_device_indicator_set(LOA_DEVICE_PAIRING);
	loa_mood_indicator_set(LOA_STATUS_OFF);
	(void)k_work_reschedule(&pairing_timeout_work, PAIRING_WINDOW);
	return start_advertising(true, false);
}
