sayhiben/little-on-air/apps/controller-esp32s3/src/receiver_link.hpp

// SPDX-License-Identifier: MIT
#pragma once
#include "controller.hpp"
#include <little_on_air/brightness.h>

enum class LinkOperation { Sync, Send, Pair, Forget, Pixel, ReadBrightness, SetBrightness };
enum class LinkPhase { Idle, Scanning, Connecting, Securing, Reading, Sending, Waiting };
struct LinkRequest {
    LinkOperation operation;
    loa_message command;
    uint8_t pixelIndex;
    loa_rgb pixelColor;
    loa_brightness brightness;
};
struct LinkResult {
    LinkRequest request;
    bool success;
    bool bonded;
    loa_message state;
    const char *error;
    bool receiverForgotten;
    loa_brightness brightness;
};

bool linkInit();
bool linkBonded();
bool linkStart(const LinkRequest &request);
bool linkPoll(LinkResult &result);
LinkPhase linkPhase();
